kittiphun-rut/MCUPR-CANTEEN/docs/interface/tft-host-03-activity.png

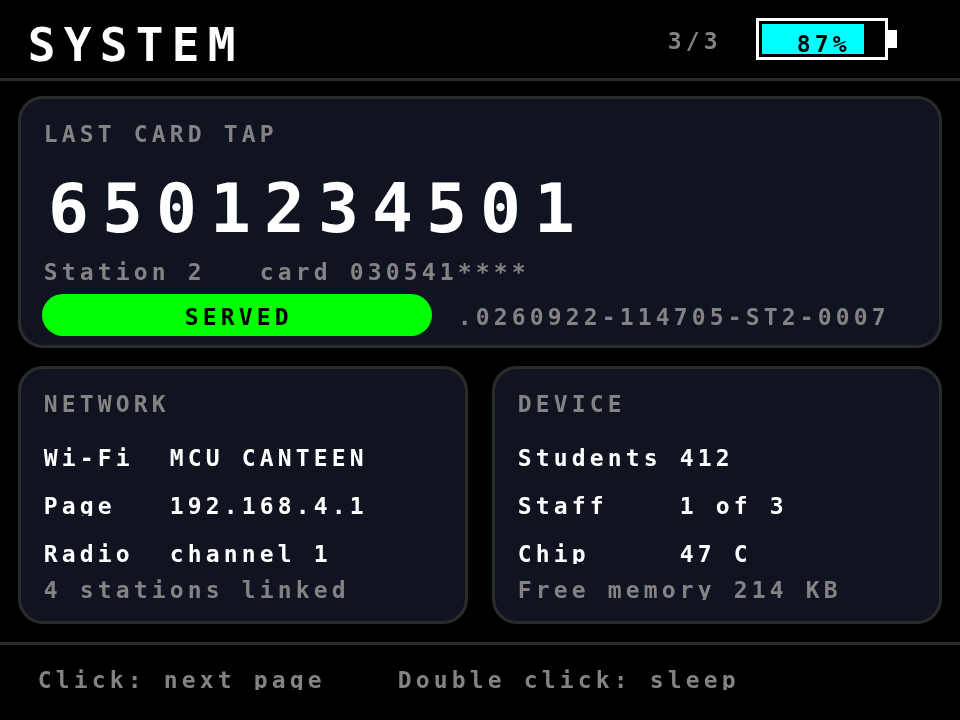
docs/interface/tft-host-03-activity.png
