kittiphun-rut/MCUPR-CANTEEN/docs/interface/tft-host-04-screensaver.png

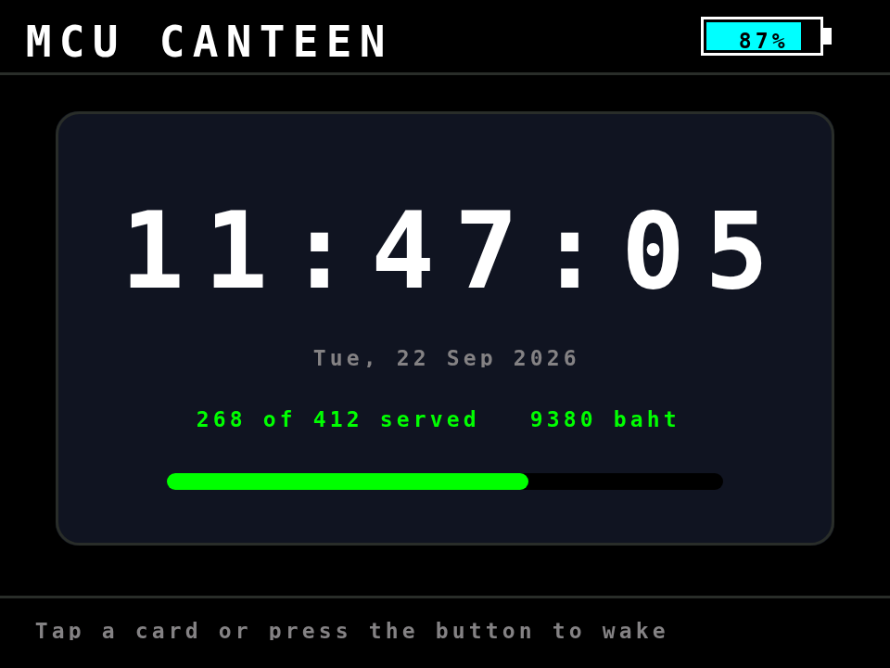
docs/interface/tft-host-04-screensaver.png
