kittiphun-rut/MCUPR-CANTEEN/docs/interface/tft-host-05-approved.png

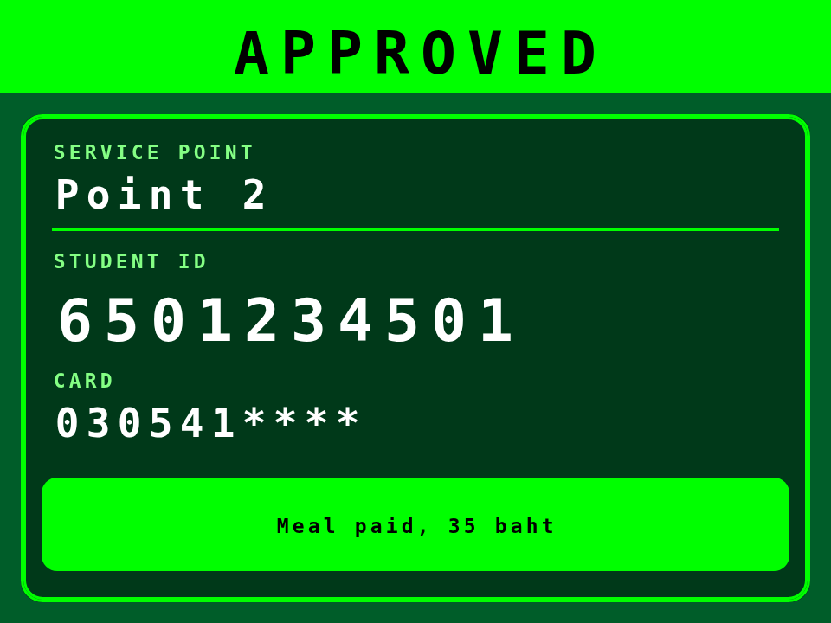
docs/interface/tft-host-05-approved.png
