kittiphun-rut/MCUPR-CANTEEN/docs/interface/tft-host-06-duplicate.png

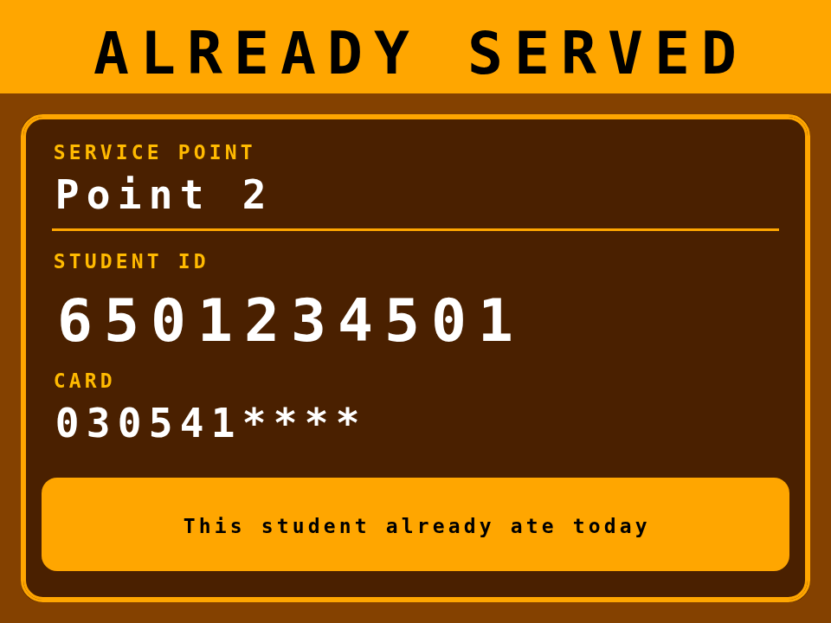
docs/interface/tft-host-06-duplicate.png
