kittiphun-rut/MCUPR-CANTEEN/docs/interface/tft-host-08-rejected.png

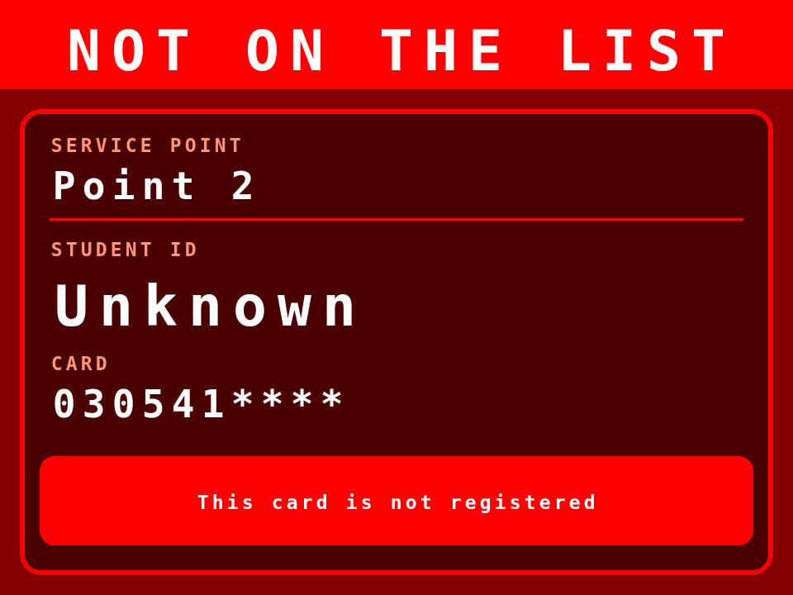
docs/interface/tft-host-08-rejected.png
