kittiphun-rut/MCUPR-CANTEEN/docs/interface/tft-host-09-bootnet-ok.png

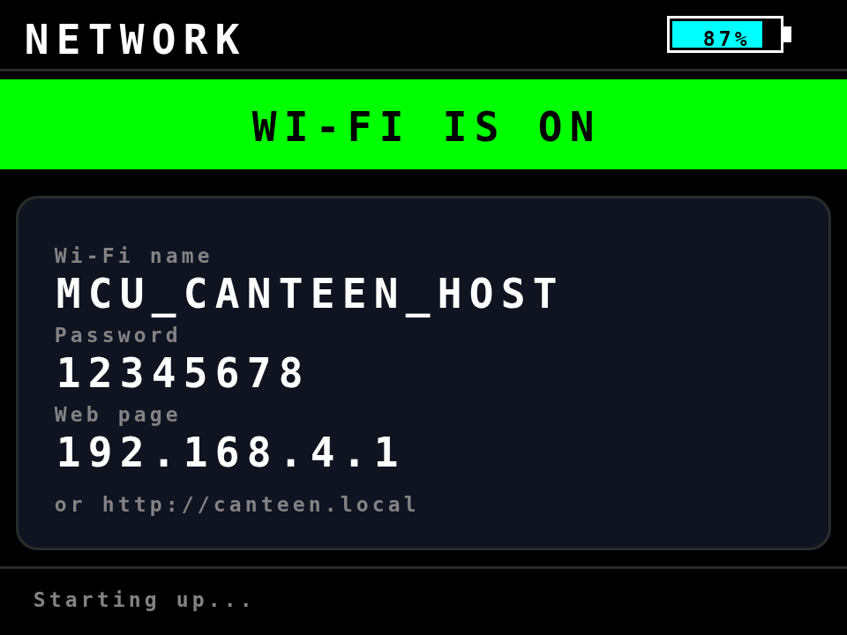
docs/interface/tft-host-09-bootnet-ok.png
