kittiphun-rut/MCUPR-CANTEEN/docs/interface/tft-host-10-bootnet-fail.png

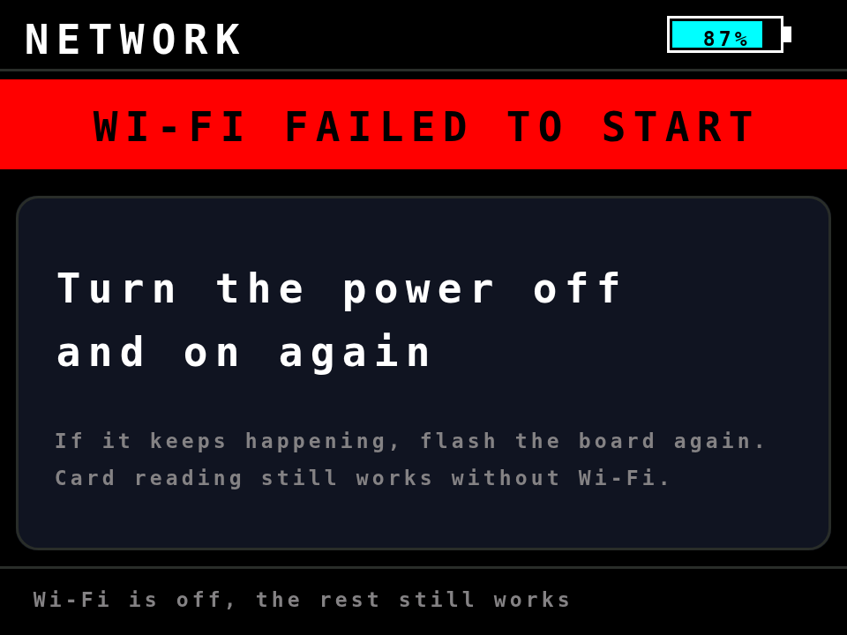
docs/interface/tft-host-10-bootnet-fail.png
