kittiphun-rut/MCUPR-CANTEEN/docs/interface/tft-host-11-credit.png

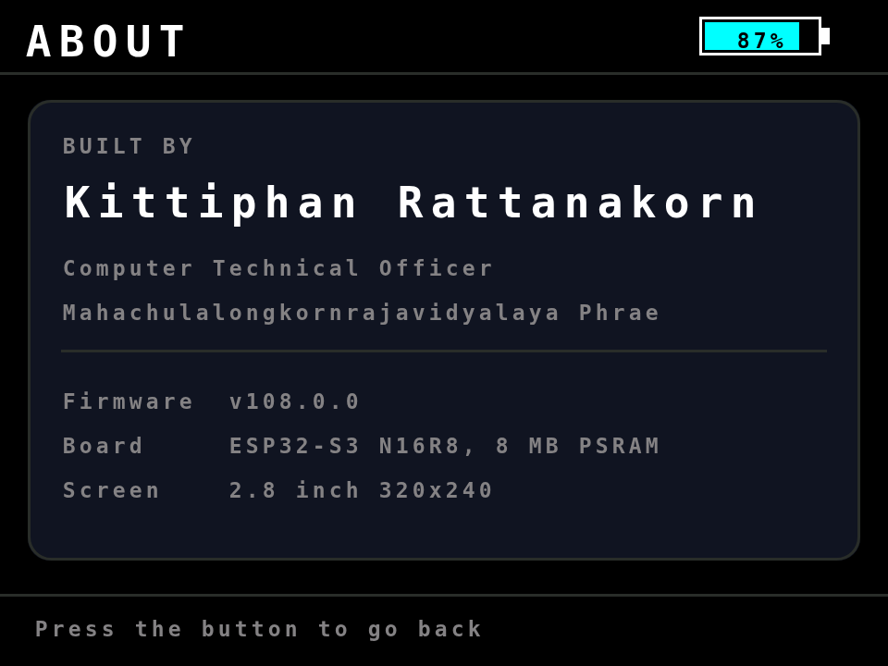
docs/interface/tft-host-11-credit.png
