kittiphun-rut/MCUPR-CANTEEN/docs/interface/tft-stn-03-diagnostics.png

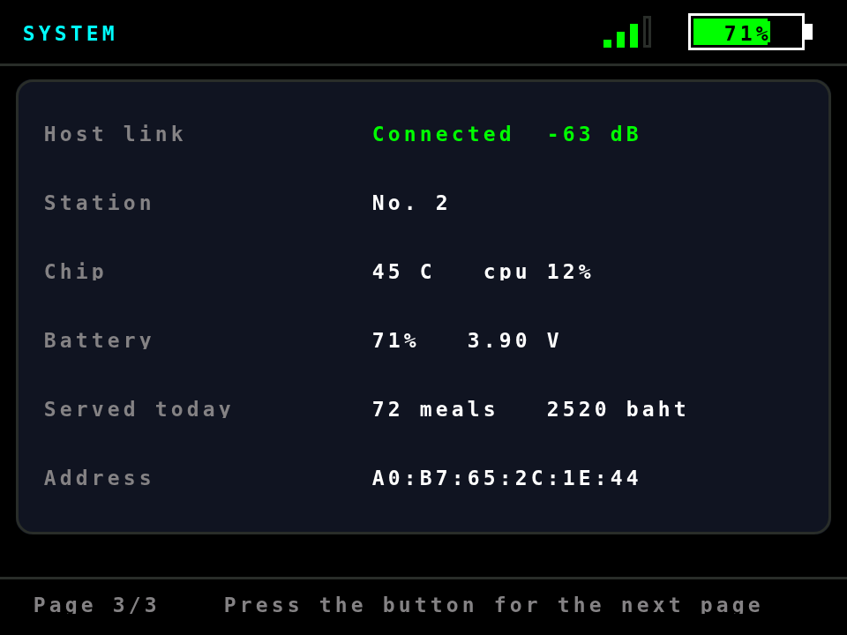
docs/interface/tft-stn-03-diagnostics.png
