kittiphun-rut/MCUPR-CANTEEN/docs/interface/tft-stn-04-screensaver.png

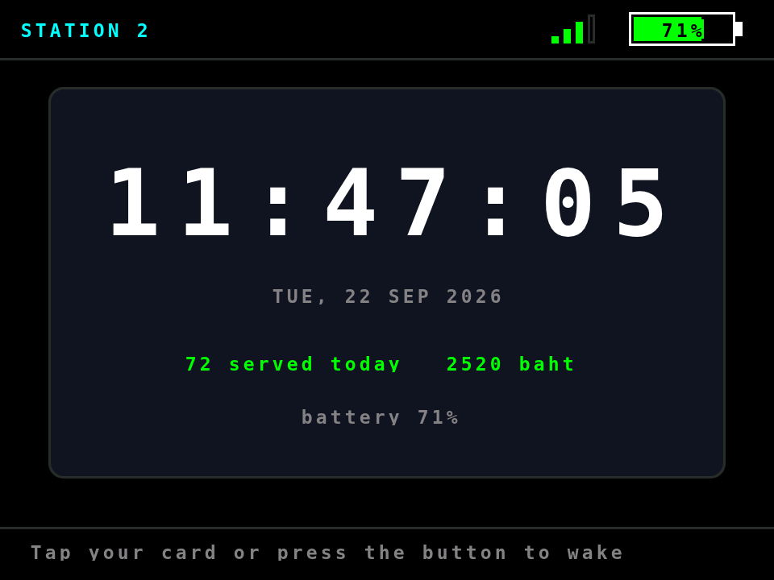
docs/interface/tft-stn-04-screensaver.png
