kittiphun-rut/MCUPR-CANTEEN/docs/interface/tft-stn-05-scanning.png

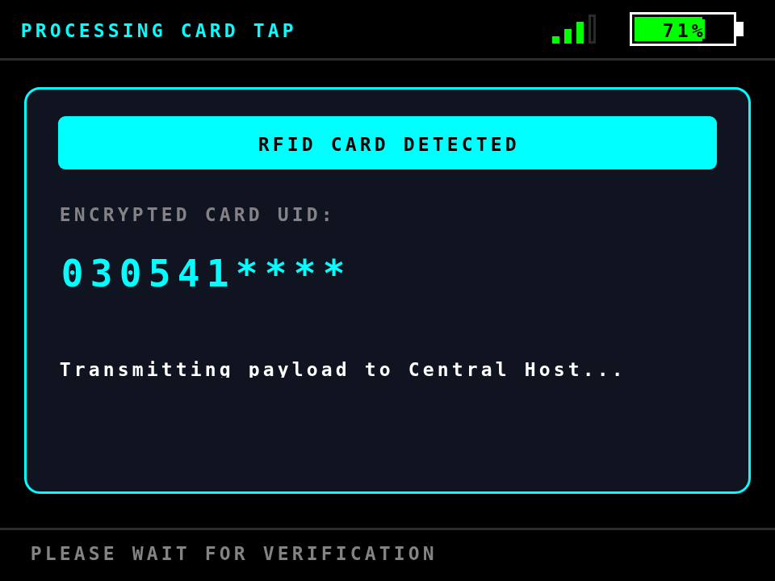
docs/interface/tft-stn-05-scanning.png
