kittiphun-rut/MCUPR-CANTEEN/docs/interface/tft-stn-07-duplicate.png

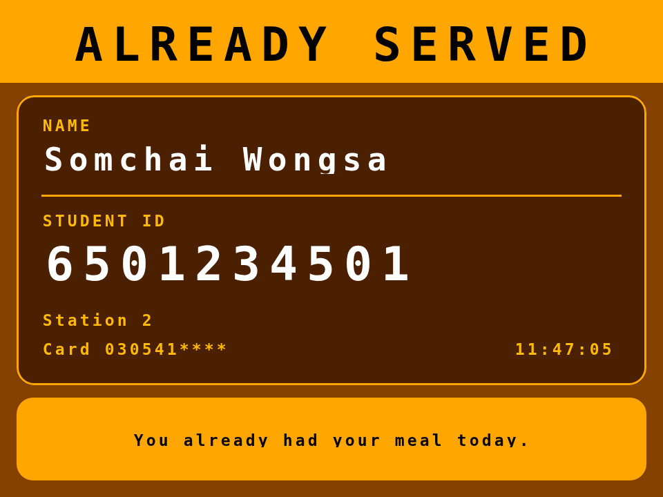
docs/interface/tft-stn-07-duplicate.png
