kittiphun-rut/MCUPR-CANTEEN/docs/interface/tft-stn-08-rejected.png

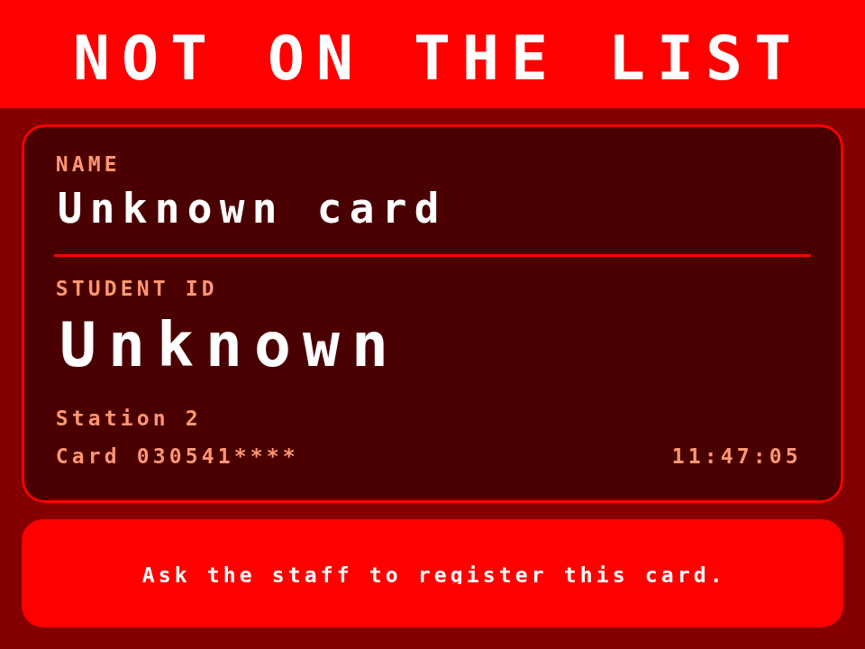
docs/interface/tft-stn-08-rejected.png
