kittiphun-rut/MCUPR-CANTEEN/docs/interface/tft-stn-09-offline.png

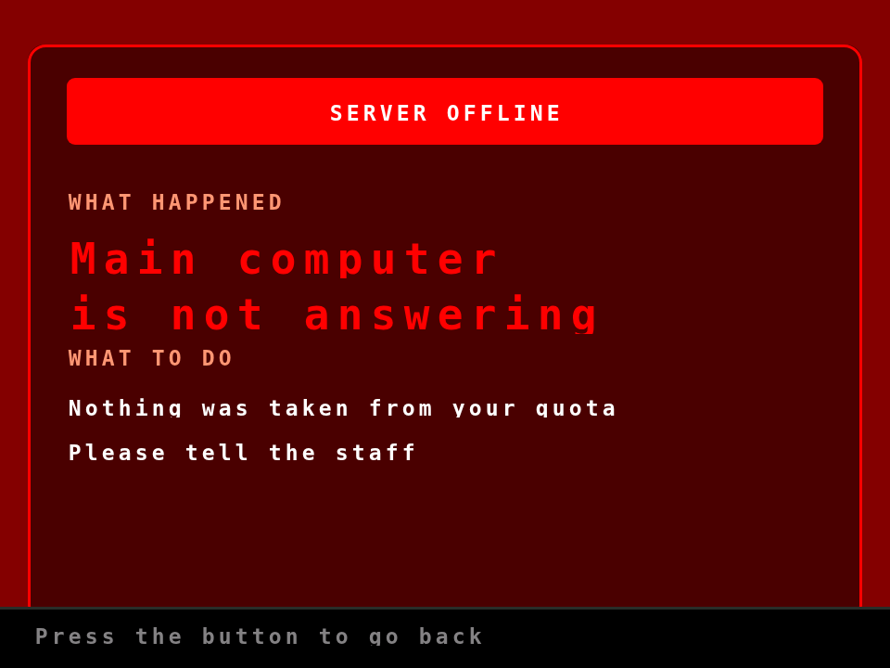
docs/interface/tft-stn-09-offline.png
