kittiphun-rut/MCUPR-CANTEEN/docs/interface/tft-stn-11-standby-light.png

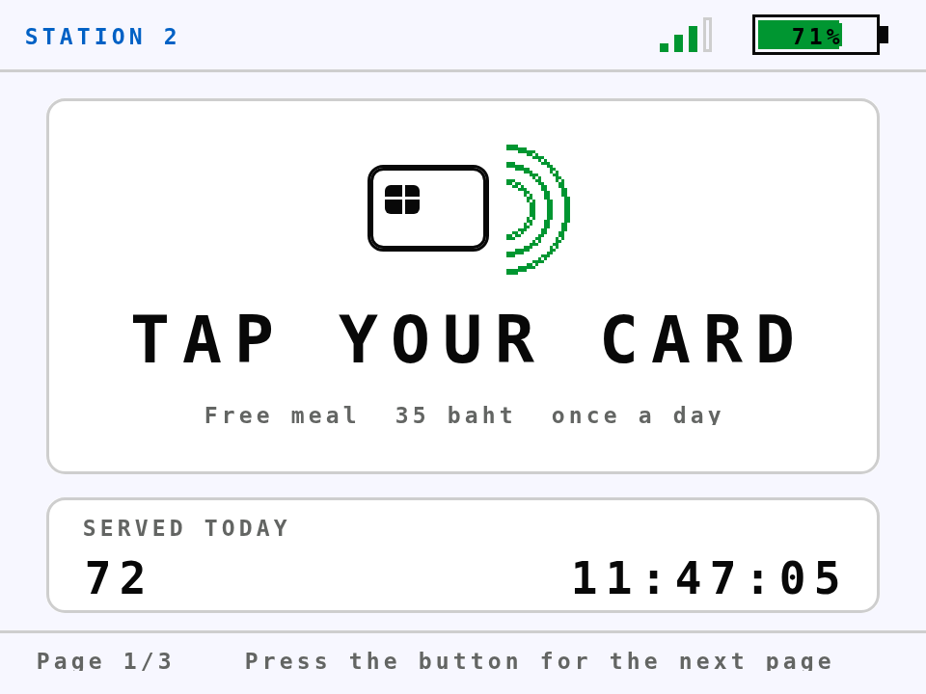
docs/interface/tft-stn-11-standby-light.png
