kittiphun-rut/MCUPR-CANTEEN/docs/interface/tft-stn-12-themelocked.png

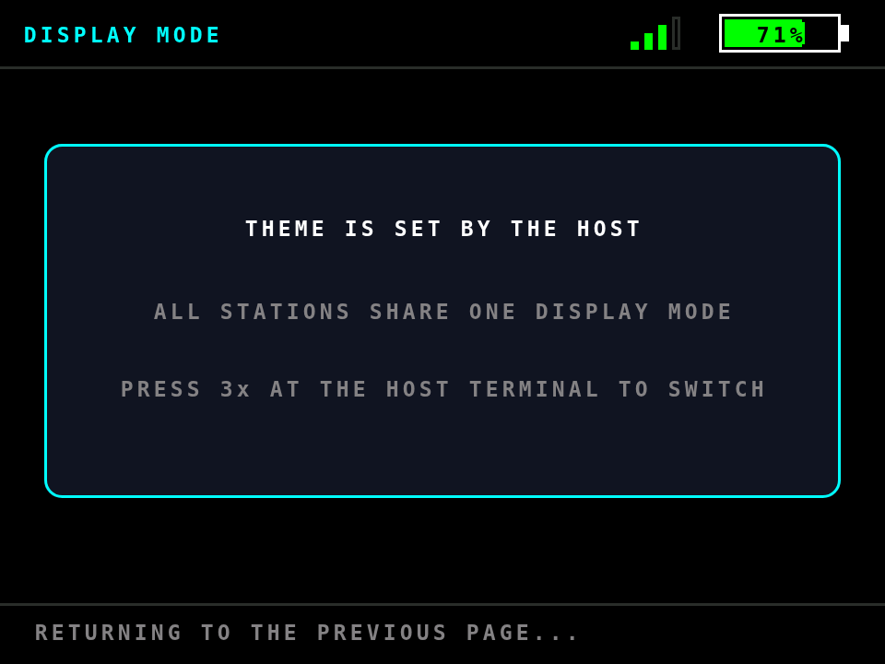
docs/interface/tft-stn-12-themelocked.png
