kittiphun-rut/MCUPR-CANTEEN/docs/interface/tft-stn-13-reader-down.png

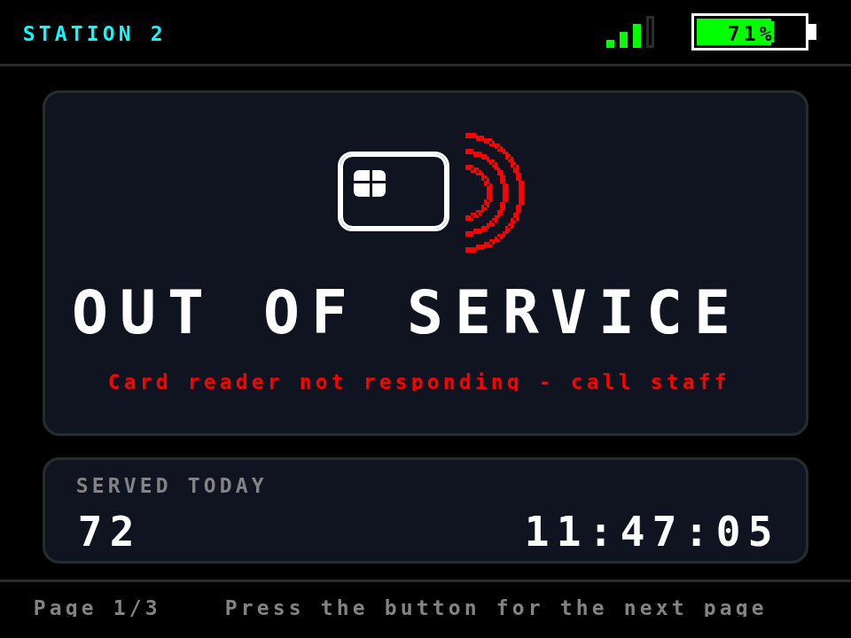
docs/interface/tft-stn-13-reader-down.png
