kittiphun-rut/MCUPR-CANTEEN/docs/interface/tft-stn-14-server-offline.png

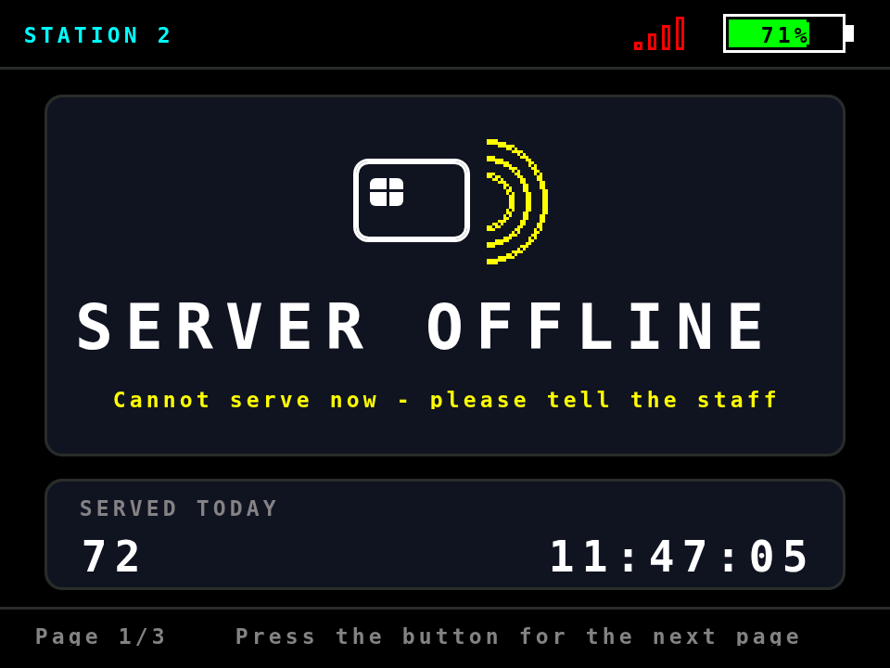
docs/interface/tft-stn-14-server-offline.png
