kittiphun-rut/MCUPR-CANTEEN/docs/interface/web-03-students.png

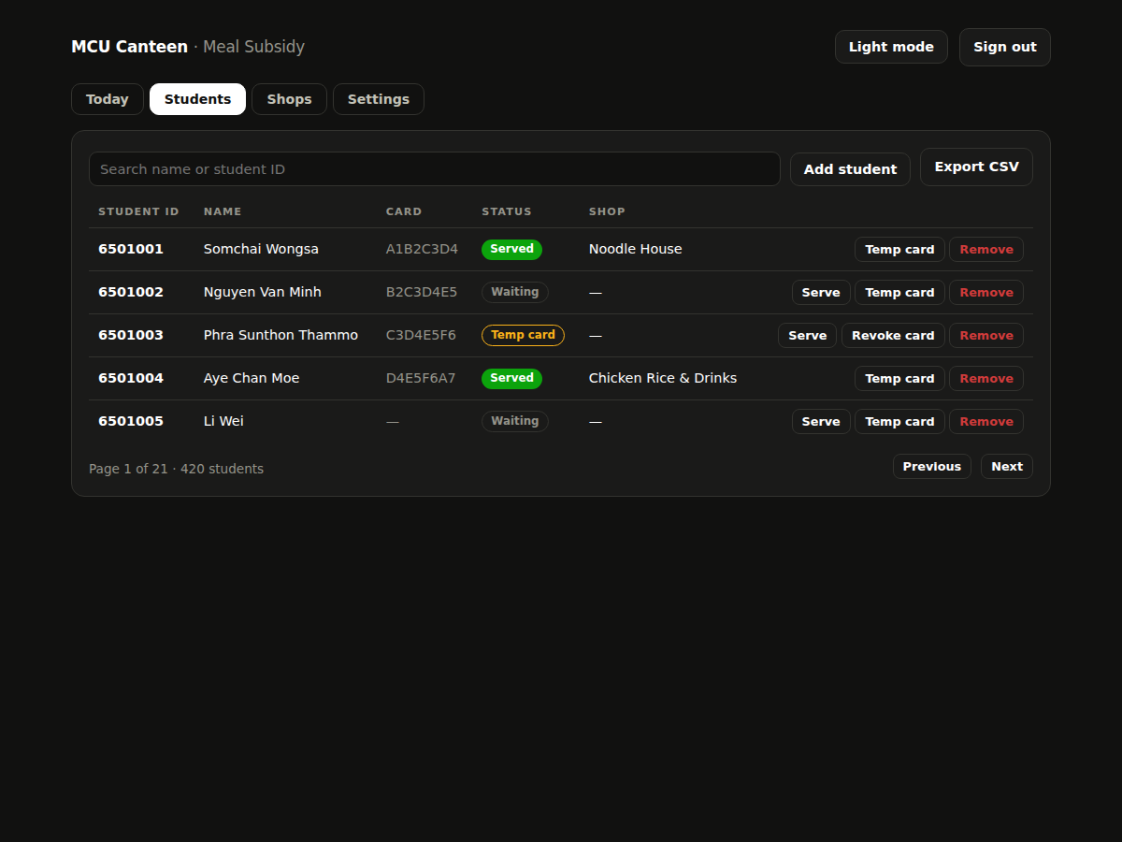
docs/interface/web-03-students.png
