kittiphun-rut/MCUPR-CANTEEN/docs/interface/web-04-shops.png

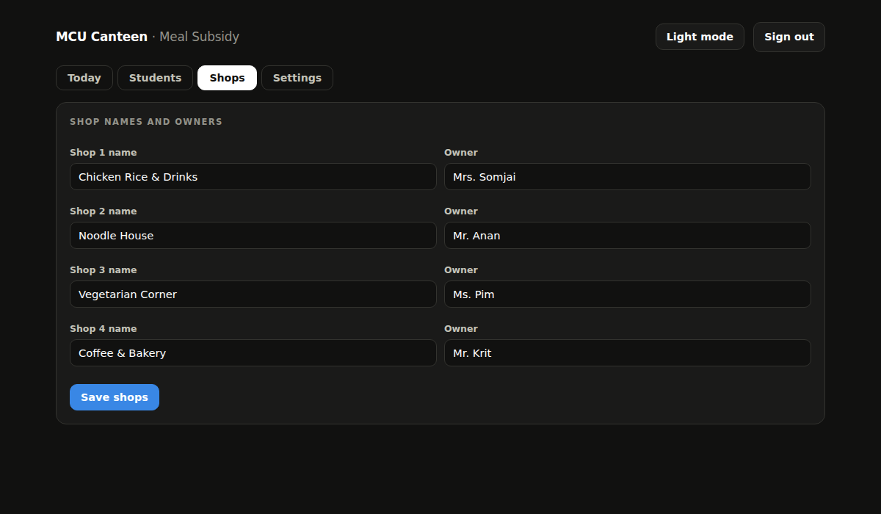
docs/interface/web-04-shops.png
