kittiphun-rut/MCUPR-CANTEEN/docs/interface/web-05-settings-light.png

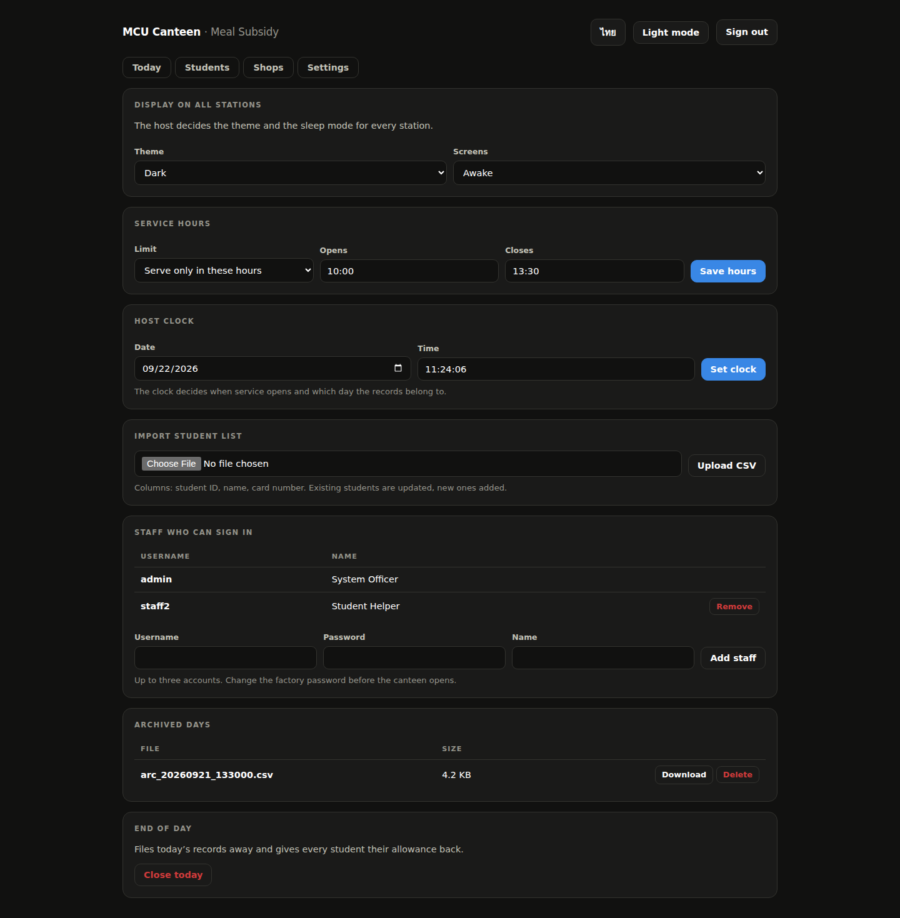
docs/interface/web-05-settings-light.png
