kittiphun-rut/MCUPR-CANTEEN/docs/interface/web-06-phone.png

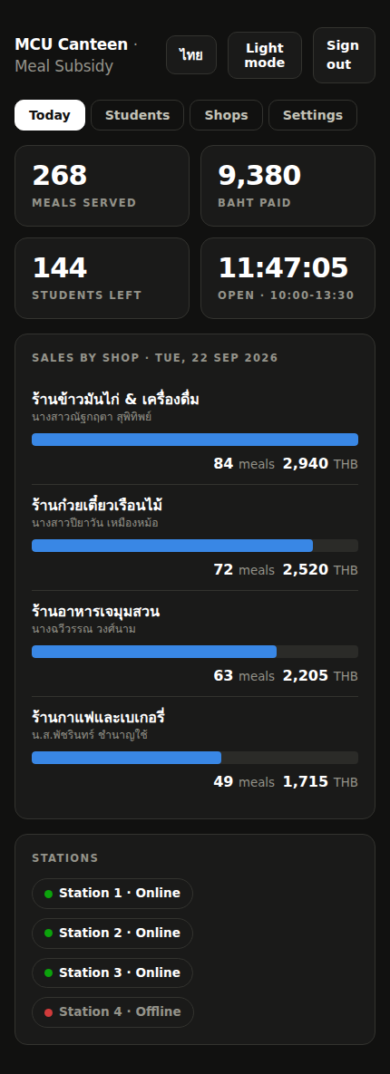
docs/interface/web-06-phone.png
