kittiphun-rut/MCUPR-CANTEEN/docs/interface/web-07-login.png

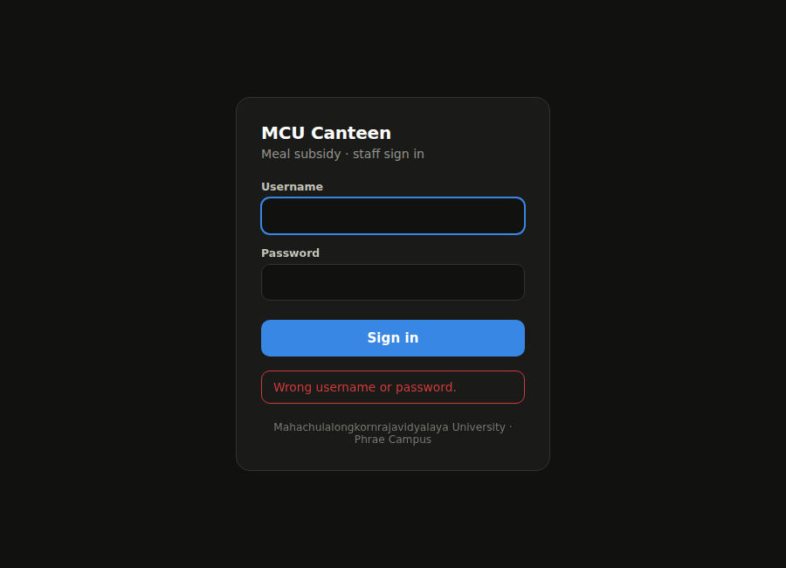
docs/interface/web-07-login.png
