kittiphun-rut/MCUPR-CANTEEN/docs/interface/web-08-today-th.png

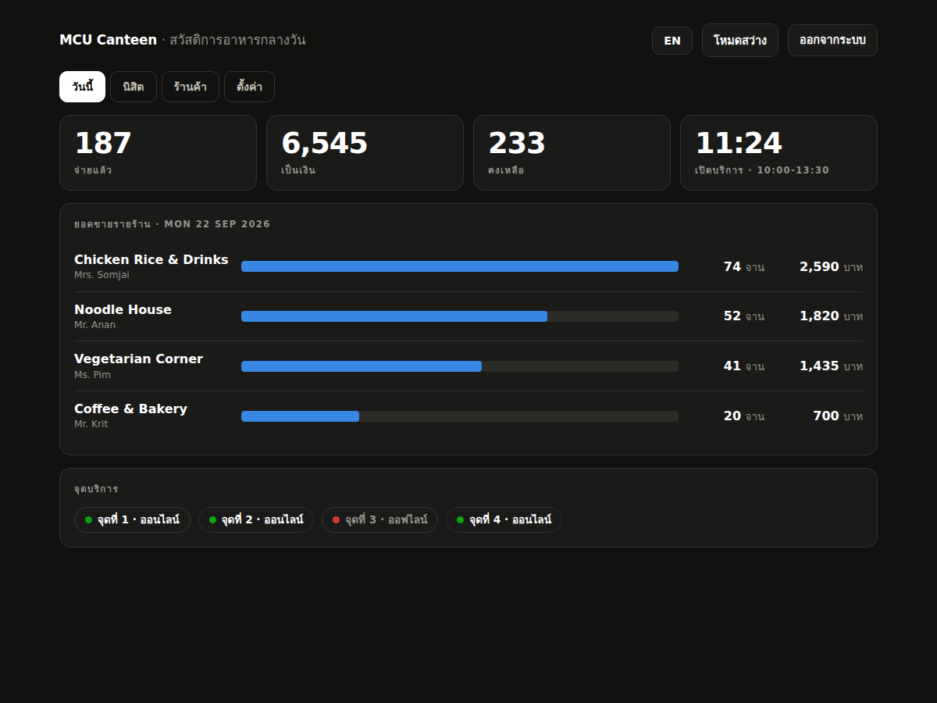
docs/interface/web-08-today-th.png
