kittiphun-rut/MCUPR-CANTEEN/docs/interface/web-10-settings-th.png

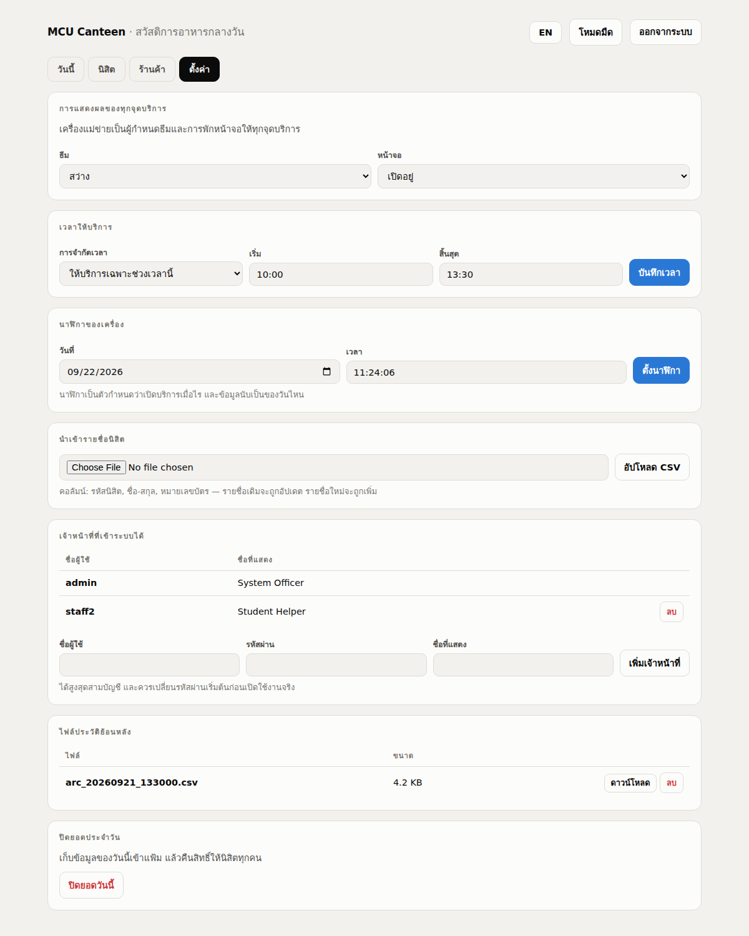
docs/interface/web-10-settings-th.png
