kittiphun-rut/MCUPR-CANTEEN/docs/interface/web-12-display-fullhd.png

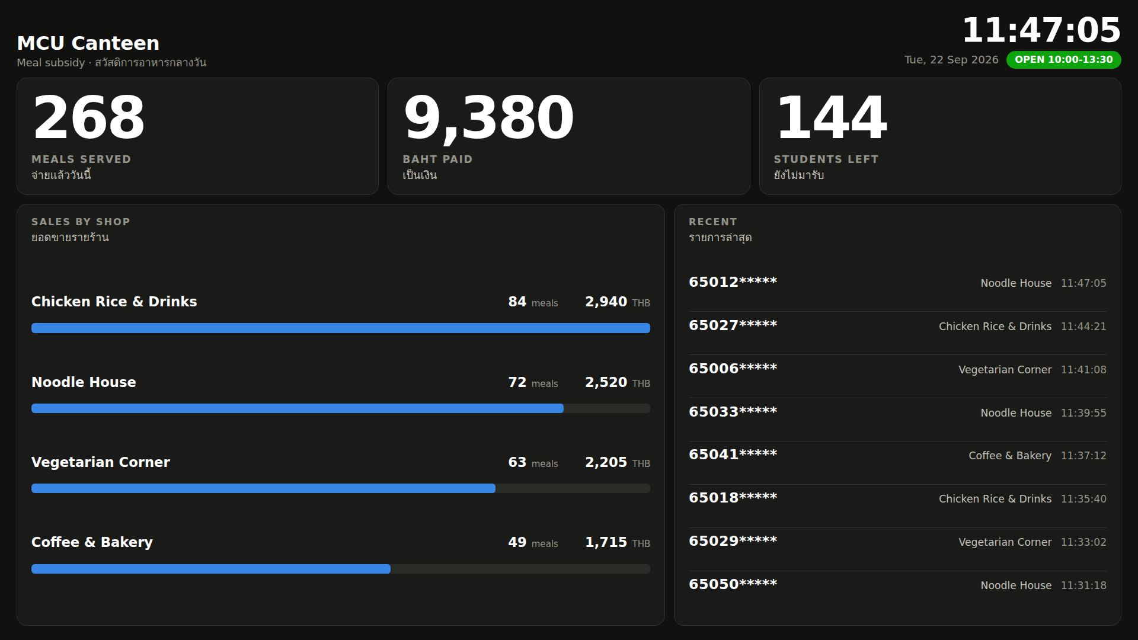
docs/interface/web-12-display-fullhd.png
