kittiphun-rut/MCUPR-CANTEEN/docs/interface/web-13-display-hd.png

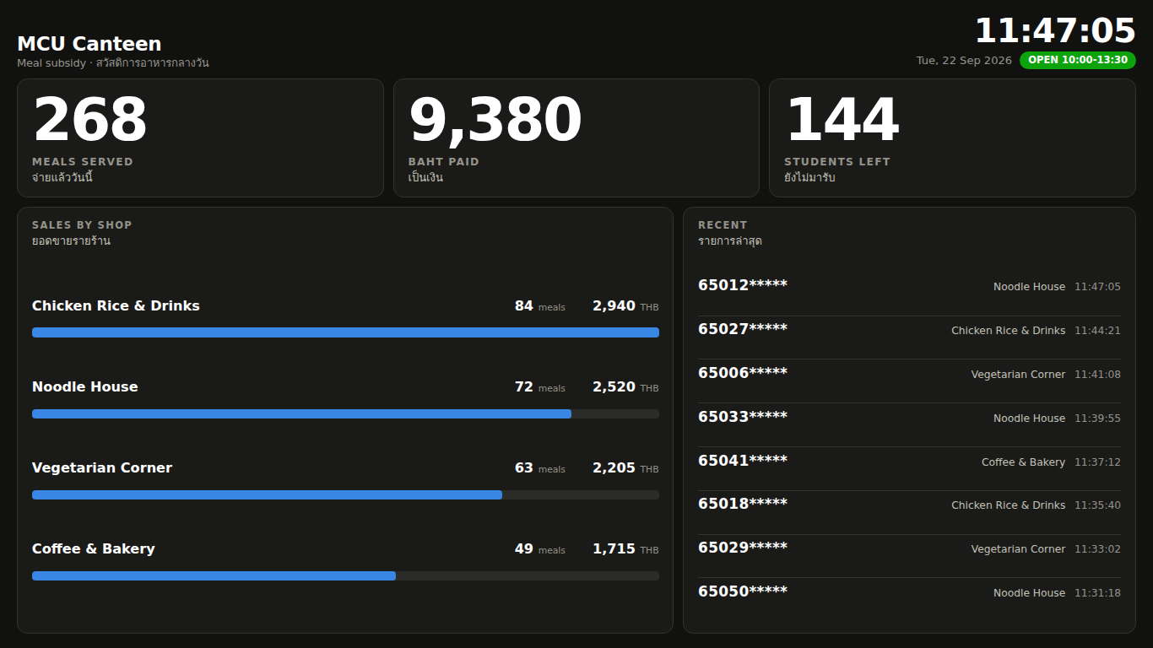
docs/interface/web-13-display-hd.png
