kittiphun-rut/MCUPR-CANTEEN/tools/screen-preview/shots/tft-host-07-timeclosed.png

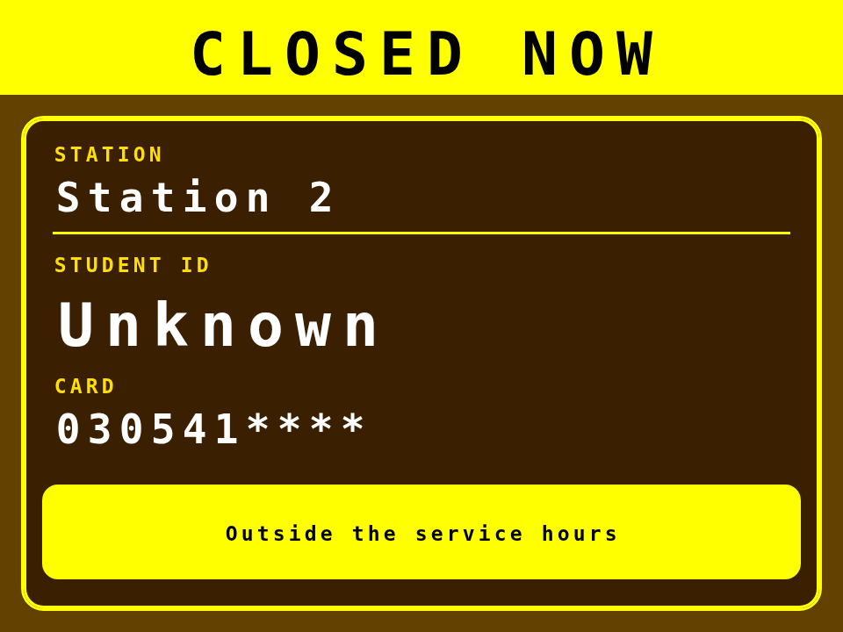
tools/screen-preview/shots/tft-host-07-timeclosed.png
