kittiphun-rut/MCUPR-CANTEEN/docs/interface/tft-stn-10-idsetup.png

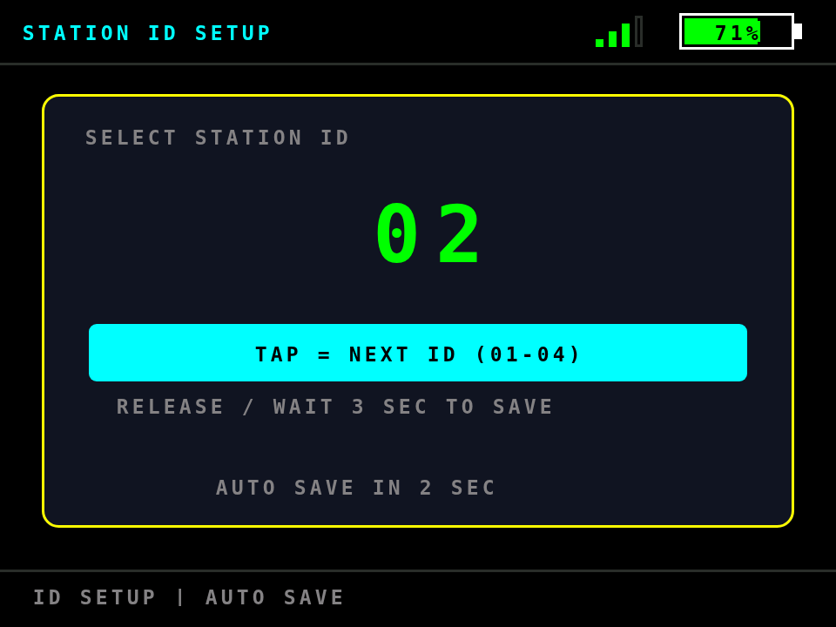
docs/interface/tft-stn-10-idsetup.png
