kittiphun-rut/MCUPR-CANTEEN/docs/interface/tft-stn-15-result-unknown.png

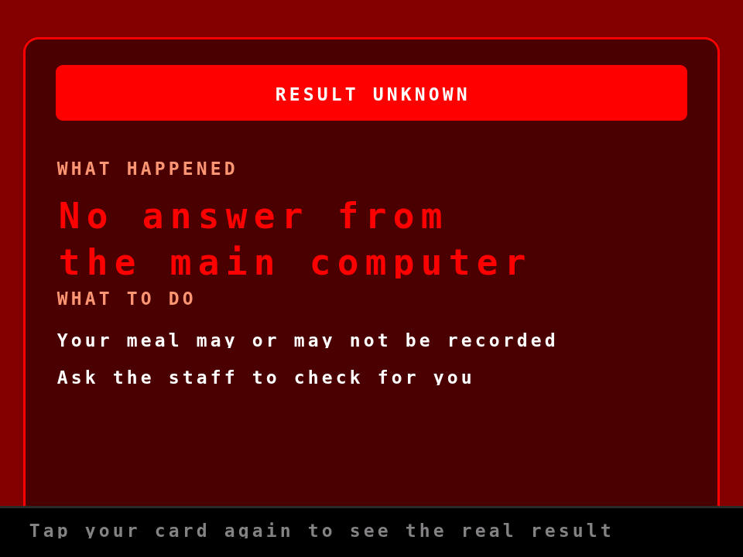
docs/interface/tft-stn-15-result-unknown.png
