kittiphun-rut/MCUPR-CANTEEN/hardware/kicad/Canteen_Station.kicad_sch

## KiCad design hardware/kicad/Canteen_Station.kicad_sch (2026-09-24)

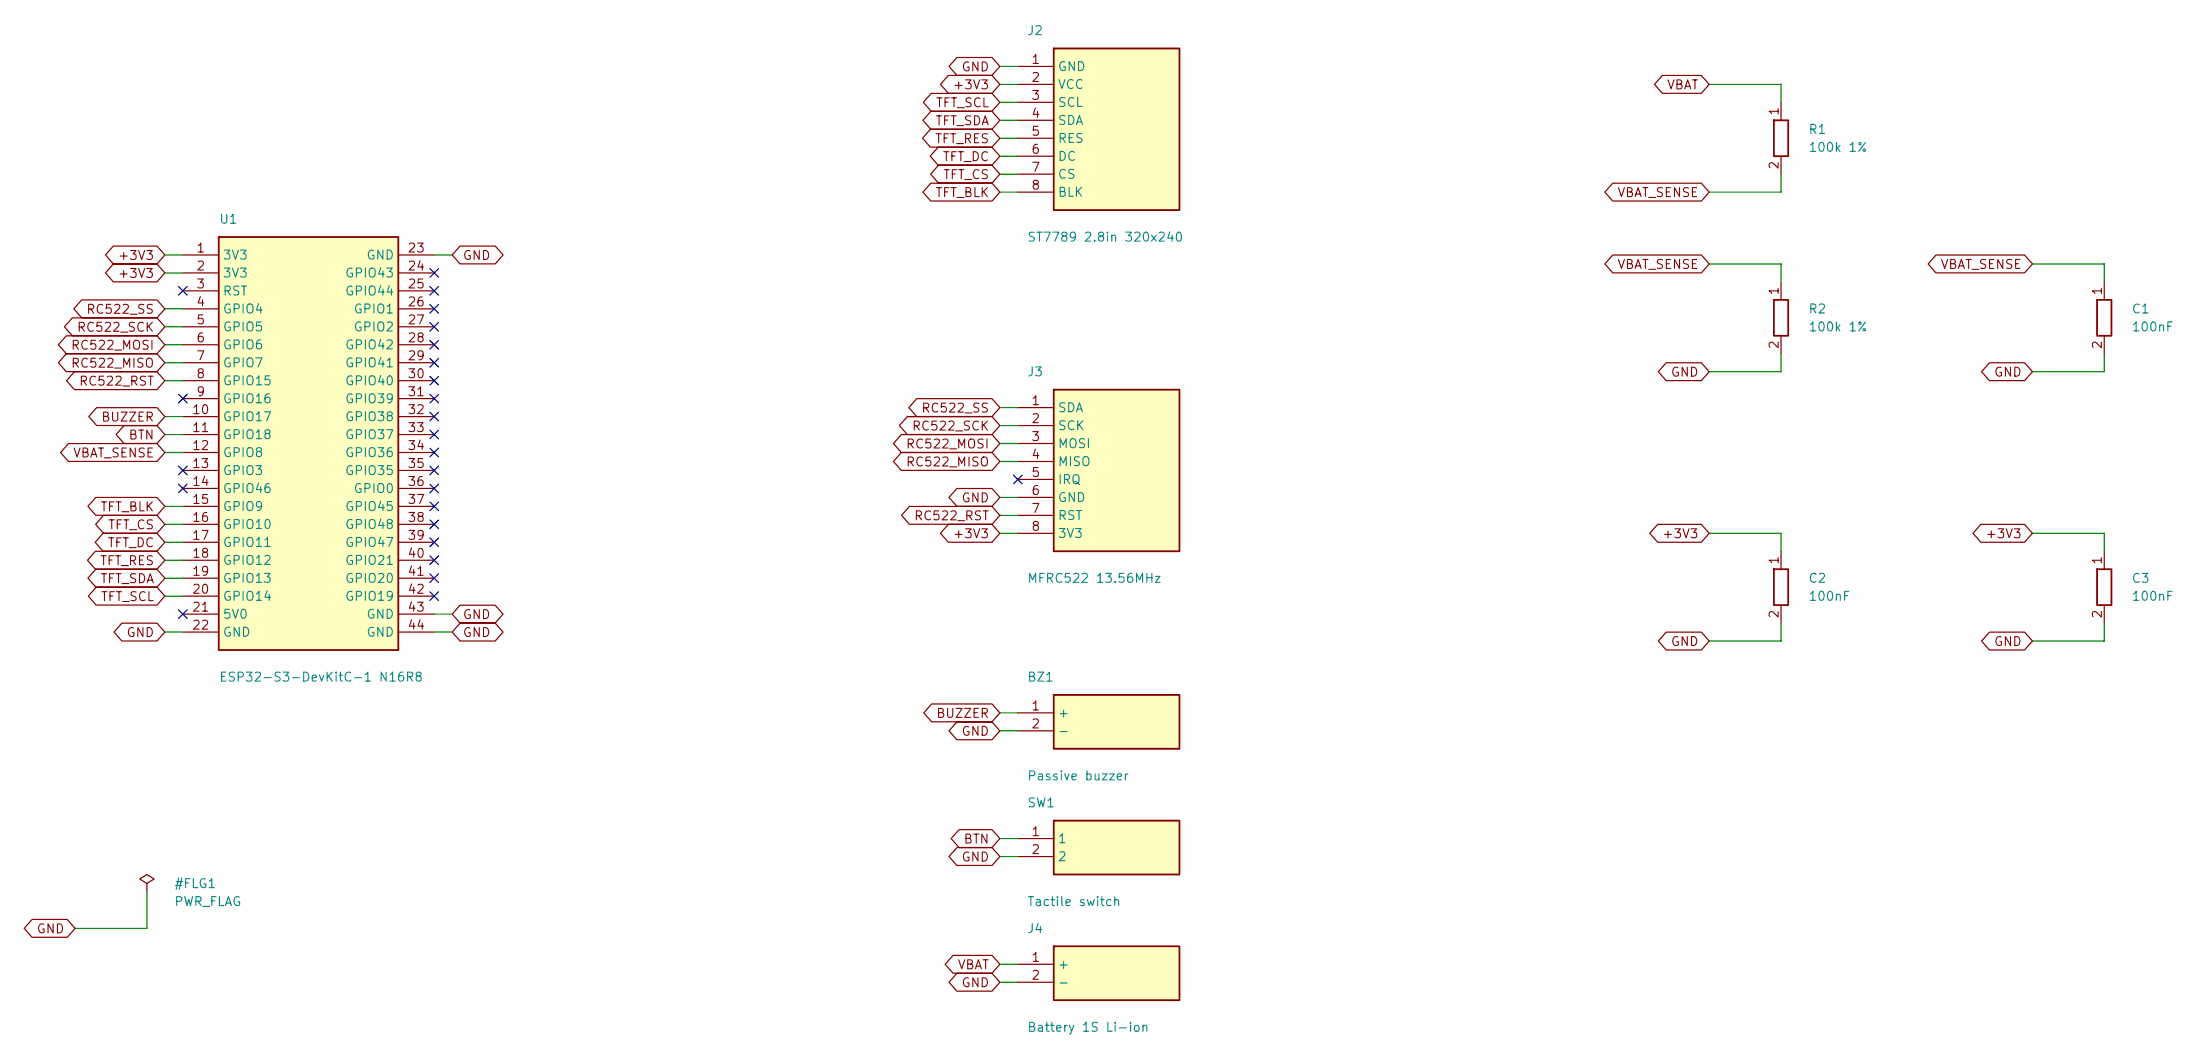
[picture p45: schematic Canteen_Station.kicad_sch]

Parts:
BZ1: Passive buzzer
C1, C2, C3: 100nF
J2: ST7789 2.8in 320x240
J3: MFRC522 13.56MHz
J4: Battery 1S Li-ion
R1, R2: 100k 1%
SW1: Tactile switch
U1: ESP32-S3-DevKitC-1 N16R8

Connections:
+3V3: C2.1, C3.1, J2.2 (VCC), J3.8 (3V3), U1.1 (3V3), U1.2 (3V3)
BTN: SW1.1, U1.11 (GPIO18)
BUZZER: BZ1.1 (+), U1.10 (GPIO17)
GND: BZ1.2 (-), C1.2, C2.2, C3.2, J2.1 (GND), J3.6 (GND), J4.2 (-), R2.2, SW1.2, U1.22 (GND), U1.23 (GND), U1.43 (GND), U1.44 (GND)
RC522_MISO: J3.4 (MISO), U1.7 (GPIO7)
RC522_MOSI: J3.3 (MOSI), U1.6 (GPIO6)
RC522_RST: J3.7 (RST), U1.8 (GPIO15)
RC522_SCK: J3.2 (SCK), U1.5 (GPIO5)
RC522_SS: J3.1 (SDA), U1.4 (GPIO4)
TFT_BLK: J2.8 (BLK), U1.15 (GPIO9)
TFT_CS: J2.7 (CS), U1.16 (GPIO10)
TFT_DC: J2.6 (DC), U1.17 (GPIO11)
TFT_RES: J2.5 (RES), U1.18 (GPIO12)
TFT_SCL: J2.3 (SCL), U1.20 (GPIO14)
TFT_SDA: J2.4 (SDA), U1.19 (GPIO13)
VBAT: J4.1 (+), R1.1
VBAT_SENSE: C1.1, R1.2, R2.1, U1.12 (GPIO8)
