kittiphun-rut/MCUPR-CANTEEN/Canteen_Host_Server/HostScreen.h

/**
 * @file      HostScreen.h
 * @brief     ทุกอย่างที่วาดลงจอ TFT ของเครื่องแม่ข่าย
 * @version   113.8.0
 * @date      2026-09-23
 * @author    Kittiphan Rattanakorn <kittiphun.rut@mcu.ac.th>
 *
 * @par Organization
 * มหาวิทยาลัยมหาจุฬาลงกรณราชวิทยาลัย วิทยาเขตแพร่
 *
 * @par Description
 * แยกออกมาจาก Canteen_Host_Server.ino เพื่อให้ไฟล์หลักสั้นและอ่านง่าย
 * นิสิตที่มารับช่วงดูแลต่อจะได้หาของเจอเร็วขึ้น
 *
 * มีสามหน้าหลักสลับด้วยปุ่มกด TODAY / SHOPS / SYSTEM
 * พร้อมหน้าพักจอ หน้าแจ้งผลการแตะบัตร หน้าแจ้งสถานะ Wi-Fi ตอนบูต และหน้าเครดิต
 *
 * ข้อความบนจอเป็นภาษาอังกฤษอย่างเดียว เพราะฟอนต์ในตัวไลบรารี Adafruit GFX
 * ไม่มีตัวอักษรไทย ส่วนหน้าเว็บเป็นสองภาษา
 *
 * @par Revision History
 * | Version | Date | Change |
 * |---|---|---|
 * | 113.8.0 | 2026-09-23 | เปลี่ยนคำว่า Point บนหน้าจอและหน้าเว็บเป็น Station ให้ตรงกับชื่อที่ใช้ทั้งระบบ ส่วนชื่อร้านยังใช้คำว่า Shop เหมือนเดิม |
 * | 113.5.0 | 2026-09-23 | จัดกึ่งกลางทุกบรรทัดบนหน้าพักจอ และให้วันที่กับช่วงเวลาอยู่บรรทัดฐานเดียวกัน |
 * | 113.4.0 | 2026-09-23 | กรองทุกข้อความให้เหลือเฉพาะ ASCII ก่อนวาด และตัดความยาวทุกช่องไม่ให้ล้นไปทับกัน |
 * | 113.3.0 | 2026-09-22 | เลิกล้างพื้นก่อนเขียนตัวอักษร ใช้การเขียนทับที่เดิมแทน จอไม่กะพริบทุกวินาทีแล้ว |
 * | 113.2.0 | 2026-09-22 | วาดซ้ำเฉพาะช่องที่ค่าเปลี่ยน ยอดรายร้านและยอดบนหน้าพักจออัปเดตเองแล้ว |
 * | 113.0.0 | 2026-09-22 | แยกออกมาจากไฟล์หลัก แล้วออกแบบหน้าจอใหม่ให้เรียบง่าย ตัวอักษรน้อย แบ่งช่องชัดเจน และรองรับสองโหมดสี |
 * | 107.0.1 | 2026-09-21 | ต้นฉบับที่ใช้เป็นจุดเริ่ม เก็บสำเนาไว้ที่ original/ |
 *
 * @warning  ถูก #include ท้ายไฟล์หลักก่อน setup() ห้ามย้ายขึ้นไปบนสุด
 * @note     Arduino IDE แสดงไฟล์นี้เป็นแท็บของสเก็ตช์เดียวกัน เปิดคู่กันได้เลย
 */

#pragma once

#include <stdarg.h>   // drawFixedText รับอาร์กิวเมนต์แบบ printf

// [113.4.0] เพิ่ม: บีบข้อความให้เหลือเฉพาะอักขระที่ฟอนต์ในตัวของจอวาดได้จริง
//
// ฟอนต์ของ Adafruit GFX มีแต่ ASCII ไบต์ตั้งแต่ 0x80 ขึ้นไปจะถูกวาดเป็นสัญลักษณ์มั่ว
// ภาษาไทยหนึ่งตัวกินสามไบต์ จึงกลายเป็นตัวประหลาดสามตัว และ **กินที่กว้างกว่าที่นับไว้
// สามเท่า** ข้อความจึงล้นกรอบไปทับของข้างเคียง เห็นเป็นอักษรซ้อนกัน
//
// ตัดทิ้งไปเลยแทนการแทนด้วยเครื่องหมายคำถาม เพราะชื่อไทยล้วนจะได้เหลือสตริงว่าง
// แล้วให้ผู้เรียกถอยไปใช้ชื่อภาษาอังกฤษสำรองได้ถูกต้อง
// [113.5.0] เพิ่ม: วาดข้อความให้อยู่กึ่งกลางแกน x โดยไม่ต้องล้างพื้นก่อน
//
// drawFixedText() เติมช่องว่างท้ายอย่างเดียว ข้อความจึงชิดซ้ายของช่องเสมอ
// พอเอาไปใช้แทนบรรทัดที่เคยจัดกึ่งกลาง ข้อความเลยเยื้องไปทางซ้าย
//
// ตัวนี้เติมช่องว่างทั้งสองข้างให้ช่องกว้างคงที่ ข้อความจึงอยู่กึ่งกลางจริง
// และช่องว่างที่เติมก็ลบของเดิมที่ยาวกว่าไปพร้อมกัน ไม่ต้องล้างพื้น ไม่กะพริบ
//
// cx คือจุดกึ่งกลางที่ต้องการ ส่วน width คือความกว้างของช่องเป็นจำนวนตัวอักษร
// ต้องกว้างพอสำหรับค่าที่ยาวที่สุดที่เป็นไปได้ ไม่งั้นจะถูกตัด
void drawCenteredText(int cx, int y, uint8_t size, uint16_t fg, uint16_t bg,
                      int width, const char* fmt, ...) {
  if (width < 1) width = 1;
  if (width > 70) width = 70;

  char raw[80];
  va_list args;
  va_start(args, fmt);
  vsnprintf(raw, sizeof(raw), fmt, args);
  va_end(args);

  int len = (int)strlen(raw);
  if (len > width) { len = width; raw[width] = '\0'; }
  int left = (width - len) / 2;

  char padded[80];
  memset(padded, ' ', sizeof(padded));
  memcpy(padded + left, raw, len);
  padded[width] = '\0';

  tft.setTextSize(size);
  tft.setTextColor(fg, bg);
  tft.setCursor(cx - (width * 6 * (int)size) / 2, y);
  tft.print(padded);
}


String asciiOnly(const String &raw) {
  String out;
  out.reserve(raw.length());
  for (unsigned int i = 0; i < raw.length(); i++) {
    uint8_t c = (uint8_t)raw[i];
    if (c >= 0x20 && c < 0x7F) out += (char)c;
  }
  out.trim();
  return out;
}


// [113.3.0] เพิ่ม: วาดข้อความทับที่เดิมโดยไม่ต้องล้างพื้นก่อน
//
// ต้นเหตุของการกะพริบคือลำดับ "ล้างพื้น แล้วค่อยเขียนตัวอักษร"
// ระหว่างสองจังหวะนั้นจอว่างเปล่าจริง ๆ ตาคนจึงเห็นเป็นการกะพริบทุกวินาที
//
// Adafruit GFX ลงสีพื้นให้ทุกตัวอักษรอยู่แล้วเมื่อกำหนดสีพื้นไว้ด้วย
// (setTextColor สองอาร์กิวเมนต์) ข้อความใหม่จึงเขียนทับของเดิมได้ในจังหวะเดียว
// ไม่มีช่วงที่จอว่าง ไม่ต้องเรียก fillRect เลย
//
// เงื่อนไขเดียวคือความยาวต้องคงที่ จึงเติมช่องว่างท้ายข้อความให้ครบ width เสมอ
// ไม่งั้นตัวอักษรเก่าที่ยาวกว่าจะค้างอยู่ เช่น 187 เปลี่ยนเป็น 9 แล้วเหลือ 87
// ใช้ %-*s ซึ่งเติมให้ครบแต่ไม่ตัดทิ้ง ค่าที่ยาวเกินคาดจึงยังแสดงครบ ไม่โกหกตัวเลข
void drawFixedText(int x, int y, uint8_t size, uint16_t fg, uint16_t bg,
                   int width, const char* fmt, ...) {
  char raw[64];
  va_list args;
  va_start(args, fmt);
  vsnprintf(raw, sizeof(raw), fmt, args);
  va_end(args);

  // ตัดให้ยาวเท่า width พอดีเสมอ ไม่ใช่แค่เติมให้ครบ
  // ถ้าปล่อยให้ยาวเกินได้ ข้อความจะล้นไปทับช่องข้างเคียง และพอรอบหน้าค่าสั้นลง
  // ช่องว่างที่เติมก็ลบของเก่าไม่หมด เหลือเป็นอักษรซ้อนกันค้างอยู่
  // ทุกช่องจึงถูกกำหนดความกว้างเผื่อไว้แล้วให้ค่าจริงยาวไม่ถึง
  char padded[72];
  snprintf(padded, sizeof(padded), "%-*.*s", width, width, raw);

  tft.setTextSize(size);
  tft.setTextColor(fg, bg);
  tft.setCursor(x, y);
  tft.print(padded);
}


// --- ชิ้นส่วนพื้นฐาน: การ์ด ป้าย แถบบน แถบล่าง ไอคอนแบตเตอรี่ ---
void drawBentoCard(int x, int y, int w, int h, uint16_t borderColor, uint16_t bgColor) {
  tft.fillRoundRect(x, y, w, h, 8, bgColor);
  tft.drawRoundRect(x, y, w, h, 8, borderColor);
}

void drawBentoPillBadge(int x, int y, int w, int h, const char* text, uint16_t fgColor, uint16_t bgColor) {
  tft.fillRoundRect(x, y, w, h, h / 2, bgColor);
  tft.setTextColor(fgColor, bgColor);
  tft.setTextSize(1);
  int textLen = strlen(text) * 6;
  int posX = x + (w - textLen) / 2;
  tft.setCursor(max(x + 2, posX), y + (h - 8) / 2);
  tft.print(text);
}

void drawHostBatteryHUD(int x, int y) {
  float volt = readHostBatteryVoltage();
  int pct = getHostBatteryPercentage(volt);

  tft.fillRect(x, y, 54, 18, getTftBg());
  tft.drawRect(x, y + 2, 44, 14, getTftTextMain());
  tft.fillRect(x + 44, y + 6, 3, 6, getTftTextMain());

  int fillWidth = (pct * 40) / 100;
  if (fillWidth < 1 && pct > 0) fillWidth = 1;

  uint16_t fillColor = (pct > 20) ? getTftAccentGreen() : getTftAccentRose();
  if (volt > 4.0f) fillColor = getTftAccentCyan();

  tft.fillRect(x + 2, y + 4, fillWidth, 10, fillColor);

  String pctStr = String(pct) + "%";
  int textWidth = pctStr.length() * 6;
  int textX = x + 2 + (40 - textWidth) / 2; 
  int textY = y + 6;

  tft.setTextSize(1);
  uint16_t textBg = (fillWidth > 22) ? fillColor : getTftBg();
  tft.setTextColor((fillWidth > 22) ? 0x0000 : getTftTextMain(), textBg);
  tft.setCursor(textX, textY);
  tft.print(pctStr);
}

void drawMiniBattery(int x, int y, int pct) {
  tft.fillRect(x, y, 26, 12, getTftCardBg());
  tft.drawRect(x, y, 22, 12, getTftTextMain());
  tft.fillRect(x + 22, y + 4, 2, 4, getTftTextMain());
  int fillW = (pct * 18) / 100;
  if (fillW < 1 && pct > 0) fillW = 1;
  uint16_t fColor = (pct > 20) ? getTftAccentGreen() : getTftAccentRose();
  tft.fillRect(x + 2, y + 2, fillW, 8, fColor);
}

void drawHostTopBar(String title, int pageNo) {
  tft.fillRect(0, 0, 320, 26, getTftBg());
  tft.drawFastHLine(0, 26, 320, getTftCardBorder());
  tft.setTextColor(getTftTextMain(), getTftBg());
  tft.setTextSize(2);
  tft.setCursor(8, 6);
  tft.print(title);
  if (pageNo > 0) {
    char tag[8];
    snprintf(tag, sizeof(tag), "%d/%d", pageNo, TOTAL_PAGES);
    tft.setTextSize(1);
    tft.setTextColor(getTftTextMuted(), getTftBg());
    tft.setCursor(222, 9);
    tft.print(tag);
  }
  drawHostBatteryHUD(252, 4);
}

void drawBentoBottomBar(String instruction) {
  tft.fillRect(0, 214, 320, 26, getTftBg());
  tft.drawFastHLine(0, 214, 320, getTftCardBorder());
  tft.setTextColor(getTftTextMuted(), getTftBg());
  tft.setTextSize(1);
  tft.setCursor(12, 222);
  tft.println(instruction);
}

// --- แอนิเมชันตอนบูต ---
void playBootAnimation() {
  setLedColor(0, 30, 60);
  tft.fillScreen(ST77XX_BLACK);
  int centerX = 160; int centerY = 110;
  for (int r = 10; r <= 85; r += 9) {
    tft.drawCircle(centerX, centerY, r, ST77XX_BLUE);
    tft.drawCircle(centerX, centerY, r + 2, ST77XX_CYAN);
    delay(20);
  }
  tft.fillScreen(ST77XX_BLACK);
  tft.drawRect(2, 2, 316, 236, ST77XX_BLUE);
  tft.drawRect(4, 4, 312, 232, ST77XX_CYAN);
  
  tft.setTextColor(ST77XX_YELLOW, ST77XX_BLACK);
  tft.setTextSize(2);
  tft.setCursor(22, 30);
  tft.println("MCU CANTEEN");
  
  tft.setTextColor(ST77XX_WHITE, ST77XX_BLACK);
  tft.setTextSize(1);
  tft.setCursor(44, 60);
  tft.println("Meal subsidy system");

  tft.setTextColor(ST77XX_GREEN, ST77XX_BLACK);
  tft.setCursor(68, 76);
  tft.printf("ESP32-S3 N16R8 | PSRAM: %d MB\n", ESP.getPsramSize() / 1024 / 1024);

  int barX = 40; int barY = 120; int barW = 240; int barH = 16;
  tft.drawRoundRect(barX - 2, barY - 2, barW + 4, barH + 4, 4, ST77XX_WHITE);
  const char* loadSteps[] = {
    "Opening storage...",
    "Loading student list...",
    "Checking the clock...",
    "Starting Wi-Fi...",
    "Ready"
  };
  for (int step = 0; step < 5; step++) {
    tft.fillRect(barX, barY + 28, barW, 14, ST77XX_BLACK);
    tft.setTextColor(ST77XX_CYAN, ST77XX_BLACK);
    tft.setTextSize(1);
    tft.setCursor(barX, barY + 28);
    tft.println(loadSteps[step]);
    int targetW = (barW * (step + 1)) / 5;
    tft.fillRoundRect(barX, barY, targetW, barH, 2, ST77XX_GREEN);
    delay(140);
  }
  soundWelcome();
  ledStandby();
  delay(200);
}

// หน้าบอกสถานะเครือข่ายตอนบูต ค้างไว้สามวินาที
// มีไว้เพราะเคยเจอปัญหาชื่อ Wi-Fi ไม่โผล่มา แล้วไม่มีอะไรบนเครื่องบอกเลยว่าเกิดอะไรขึ้น
// [113.0.0] เพิ่ม: บอกสถานะ Wi-Fi ตอนบูต ค้างไว้สามวินาที
//           เคยเจอปัญหาชื่อ Wi-Fi ไม่โผล่มา แล้วไม่มีอะไรบนเครื่องบอกว่าเกิดอะไรขึ้น
void showBootNetworkStatus() {
  tft.fillScreen(getTftBg());
  drawHostTopBar("NETWORK");

  uint16_t tone = hostApReady ? getTftAccentGreen() : getTftAccentRose();
  tft.fillRect(0, 30, 320, 34, tone);
  const char* head = hostApReady ? "WI-FI IS ON" : "WI-FI FAILED TO START";
  tft.setTextSize(2);
  tft.setTextColor(isTftDarkMode ? 0x0000 : BENTO_WHITE, tone);
  tft.setCursor(max(4, (320 - (int)strlen(head) * 12) / 2), 39);
  tft.print(head);

  drawBentoCard(6, 74, 308, 134, getTftCardBorder(), getTftCardBg());
  tft.setTextSize(1);
  if (hostApReady) {
    tft.setTextColor(getTftTextMuted(), getTftCardBg());
    tft.setCursor(20, 92);  tft.print("Wi-Fi name");
    tft.setCursor(20, 122); tft.print("Password");
    tft.setCursor(20, 152); tft.print("Web page");
    tft.setTextColor(getTftTextMain(), getTftCardBg());
    tft.setTextSize(2);
    tft.setCursor(20, 102); tft.print(default_ap_ssid);
    tft.setCursor(20, 132); tft.print(default_ap_pass);
    tft.setCursor(20, 162); tft.print(WiFi.softAPIP().toString());
    tft.setTextSize(1);
    tft.setTextColor(getTftTextMuted(), getTftCardBg());
    tft.setCursor(20, 186); tft.printf("or http://%s.local", mdns_hostname);
  } else {
    tft.setTextColor(getTftTextMain(), getTftCardBg());
    tft.setTextSize(2);
    tft.setCursor(20, 100); tft.print("Turn the power off");
    tft.setCursor(20, 124); tft.print("and on again");
    tft.setTextSize(1);
    tft.setTextColor(getTftTextMuted(), getTftCardBg());
    tft.setCursor(20, 162); tft.print("If it keeps happening, flash the board again.");
    tft.setCursor(20, 176); tft.print("Card reading still works without Wi-Fi.");
    soundBeep();
  }

  drawBentoBottomBar(hostApReady ? "Starting up..." : "Wi-Fi is off, the rest still works");
  delay(3000);
}

// --- ชิ้นส่วนเพิ่มเติมสำหรับหน้าจอแบบใหม่ ---

// [113.0.0] เพิ่ม: ชุดชิ้นส่วนสำหรับหน้าจอแบบใหม่
// ตัดข้อความให้พอดีความกว้างที่ให้มา (ฟอนต์ในตัวกว้างตัวละ 6 พิกเซลต่อขนาด 1)
// [113.4.0] เพิ่ม: ชื่อร้านสำหรับขึ้นจอ ลำดับการถอย ชื่ออังกฤษ > ส่วน ASCII ของชื่อจริง > Shop N
//           ประกันว่าจอจะไม่มีวันได้รับข้อความที่ฟอนต์วาดไม่ได้
String shopScreenName(int i) {
  String s = asciiOnly(shops[i].screen);
  if (s.length() == 0) s = asciiOnly(shops[i].name);
  if (s.length() == 0) s = "Shop " + String(i + 1);
  return s;
}

String fitLabel(const String &raw, int maxChars) {
  if ((int)raw.length() <= maxChars) return raw;
  if (maxChars <= 1) return raw.substring(0, maxChars);
  return raw.substring(0, maxChars - 1) + ".";
}

// หัวข้อเล็ก ๆ มุมบนซ้ายของการ์ด บอกว่าการ์ดนี้คืออะไร
void drawCardLabel(int x, int y, const char* label) {
  tft.setTextColor(getTftTextMuted(), getTftCardBg());
  tft.setTextSize(1);
  tft.setCursor(x, y);
  tft.print(label);
}

// จุดกลมบอกสถานะ ใช้แทนคำว่า ONLINE/OFFLINE ที่ยาวเกินไป
void drawStatusDot(int cx, int cy, bool good) {
  tft.fillCircle(cx, cy, 4, good ? getTftAccentGreen() : getTftAccentRose());
}

// แถบความคืบหน้า ใช้บอกว่าวันนี้จ่ายไปแล้วกี่ส่วนของทั้งหมด
void drawProgressBar(int x, int y, int w, int h, int pct) {
  if (pct < 0) pct = 0;
  if (pct > 100) pct = 100;
  // [113.3.0] แก้: สี่เหลี่ยมมุมโค้งไม่ลงสีที่มุมทั้งสี่ ค่าเก่าจึงค้างอยู่ตรงนั้น
  //           ล้างกรอบสี่เหลี่ยมเต็มก่อนหนึ่งครั้ง แถบนี้วาดเฉพาะตอนยอดเปลี่ยน
  //           ไม่ได้วาดทุกวินาที จึงไม่ทำให้กะพริบ
  tft.fillRect(x, y, w, h, getTftCardBg());
  tft.fillRoundRect(x, y, w, h, h / 2, getTftBg());
  int fillW = (w * pct) / 100;
  if (fillW < 2 && pct > 0) fillW = 2;
  if (fillW > 0) tft.fillRoundRect(x, y, fillW, h, h / 2, getTftAccentGreen());
}

// --- หน้าจอเต็ม: สามหน้าหลัก โหมดพักจอ ผลการสแกน และหน้าเครดิต ---
// ออกแบบใหม่ให้คนที่ไม่ใช่ช่างอ่านออกในสายตาเดียว
// หน้า 1 ยอดวันนี้ | หน้า 2 ร้านค้าและจุดบริการ | หน้า 3 ข้อมูลเครื่อง
// [113.0.0] แก้: ออกแบบสามหน้าหลักใหม่ให้คนที่ไม่ใช่ช่างอ่านออกในสายตาเดียว
//           หน้า 1 ยอดวันนี้ | หน้า 2 ร้านค้าและจุดบริการ | หน้า 3 ข้อมูลเครื่อง
void renderHostPage(bool fullRedraw) {
  if (isLiveScanDisplaying) return;
  if (isCreditActive) { renderDeveloperCredit(); return; }
  if (isScreensaverActive) { renderScreensaver(fullRedraw); return; }
  if (currentHostPage < 0 || currentHostPage >= TOTAL_PAGES) currentHostPage = 0;

  ledStandby();

  int usedCount = 0;
  int shopCounts[4] = {0, 0, 0, 0};
  for (const auto& s : db) {
    if (s.claimed) {
      usedCount++;
      if (s.station >= 1 && s.station <= 4) shopCounts[s.station - 1]++;
    }
  }

  if (fullRedraw) tft.fillScreen(getTftBg());

  // ==========================================================================
  // หน้า 1 — ยอดวันนี้ สามช่องใหญ่ ตัวเลขโต ๆ อ่านจากไกลได้
  // ==========================================================================
  if (currentHostPage == 0) {
    if (fullRedraw) {
      drawHostTopBar("TODAY", 1);
      drawBentoCard(6, 32, 150, 88, getTftCardBorder(), getTftCardBg());
      drawCardLabel(14, 40, "MEALS SERVED");
      drawBentoCard(164, 32, 150, 88, getTftCardBorder(), getTftCardBg());
      drawCardLabel(172, 40, "BAHT PAID");
      drawBentoCard(6, 126, 308, 82, getTftCardBorder(), getTftCardBg());
      drawCardLabel(14, 134, "SERVICE");
      drawBentoBottomBar("Click: next page    Double click: sleep");
    }

    // [113.2.0] แก้: วาดซ้ำเฉพาะช่องที่ค่าเปลี่ยนจริง ของเดิมล้างแล้ววาดใหม่ทุกวินาที
    //           ทั้งที่ตัวเลขส่วนใหญ่ไม่ได้เปลี่ยน จอจึงกะพริบตลอดเวลา
    static int lastUsed = -1, lastTotal = -1;
    static String lastClock = "", lastDate = "";
    static int lastOpen = -1;

    // ช่องซ้าย: จำนวนจานที่จ่ายไปแล้ว พร้อมแถบความคืบหน้า
    if (fullRedraw || usedCount != lastUsed || (int)db.size() != lastTotal) {
      drawFixedText(14, 56, 4, getTftTextMain(), getTftCardBg(), 4, "%d", usedCount);
      drawFixedText(14, 92, 1, getTftTextMuted(), getTftCardBg(), 20,
                    "of %d students", (int)db.size());
      int pct = (db.size() > 0) ? (usedCount * 100) / (int)db.size() : 0;
      drawProgressBar(14, 106, 134, 6, pct);

      // ช่องขวา: เป็นเงินเท่าไร เปลี่ยนพร้อมกันกับจำนวนจานเสมอ
      drawFixedText(172, 56, 4, getTftAccentGreen(), getTftCardBg(), 5, "%d", usedCount * 35);
      drawFixedText(172, 92, 1, getTftTextMuted(), getTftCardBg(), 20, "35 baht per student");

      lastUsed = usedCount;
      lastTotal = (int)db.size();
    }

    // ช่องล่าง: นาฬิกาเดินทุกวินาที จึงเป็นจุดที่คนเห็นการกะพริบชัดที่สุด
    // เขียนทับที่เดิมอย่างเดียว ไม่ล้างพื้นก่อน รูปแบบ HH:MM:SS ยาวคงที่แปดตัวเสมอ
    String nowClock = getTimeOnlyStr();
    if (fullRedraw || nowClock != lastClock) {
      drawFixedText(14, 150, 4, getTftTextMain(), getTftCardBg(), 8, "%s", nowClock.c_str());
      lastClock = nowClock;
    }

    String nowDate = getDateFormattedStr();
    if (fullRedraw || nowDate != lastDate) {
      drawFixedText(14, 186, 1, getTftTextMuted(), getTftCardBg(), 24, "%s", nowDate.c_str());
      lastDate = nowDate;
    }

    bool isOpen = isWithinServiceTime();
    if (fullRedraw || (int)isOpen != lastOpen) {
      char hours[16];
      snprintf(hours, sizeof(hours), "%02d:%02d-%02d:%02d",
               serviceStartHour, serviceStartMin, serviceEndHour, serviceEndMin);
      tft.fillRect(210, 148, 100, 48, getTftCardBg());
      drawBentoPillBadge(214, 152, 94, 22, isOpen ? "OPEN" : "CLOSED",
                         isTftDarkMode ? 0x0000 : BENTO_WHITE,
                         isOpen ? getTftAccentGreen() : getTftAccentRose());
      tft.setTextColor(getTftTextMuted(), getTftCardBg());
      tft.setTextSize(1);
      // ให้อยู่บรรทัดฐานเดียวกับวันที่ทางซ้าย จะได้ดูเป็นแถวเดียวกัน
      tft.setCursor(214 + (94 - (int)strlen(hours) * 6) / 2, 186);
      tft.print(hours);
      lastOpen = (int)isOpen;
    }
  }
  // ==========================================================================
  // หน้า 2 — ร้านค้าและจุดบริการ สี่ช่อง เจ้าของร้านดูยอดของตัวเองได้ทันที
  // ==========================================================================
  else if (currentHostPage == 1) {
    if (fullRedraw) {
      drawHostTopBar("SHOPS", 2);
      drawBentoBottomBar("Click: next page    Double click: sleep");
    }

    int coords[4][2] = { {6, 32}, {164, 32}, {6, 122}, {164, 122} };
    static int waitDots = 0;
    if (!fullRedraw) waitDots = (waitDots + 1) % 4;

    for (int i = 0; i < 4; i++) {
      int x = coords[i][0], y = coords[i][1], w = 150, h = 86;

      if (fullRedraw) {
        drawBentoCard(x, y, w, h, getTftCardBorder(), getTftCardBg());

        // ชื่อร้านมาก่อน เพราะเจ้าของร้านมองหาชื่อตัวเอง ไม่ได้มองหาเลขจุดบริการ
        // เต็มความกว้างการ์ด ไม่มีอะไรมาวาดทับภายหลัง
        // ชื่อร้านเปลี่ยนได้เฉพาะตอนบันทึกจากหน้าเว็บ ซึ่งสั่งวาดใหม่ทั้งจออยู่แล้ว
        tft.setTextColor(getTftTextMain(), getTftCardBg());
        tft.setTextSize(1);
        // [113.4.0] แก้: เดิมเอาชื่อร้านภาษาไทยมาวาดตรง ๆ จอจึงขึ้นสัญลักษณ์มั่ว
        //           และกว้างกว่าที่นับไว้จนล้นไปทับของข้างเคียง
        drawFixedText(x + 8, y + 7, 1, getTftTextMain(), getTftCardBg(), 22,
                      "%s", shopScreenName(i).c_str());
      }

      // [113.2.0] แก้: ยอดของร้านเคยวาดเฉพาะตอนวาดใหม่ทั้งจอ พอมีคนมารับอาหาร
      //           ขณะเปิดหน้านี้ค้างไว้ ตัวเลขจึงไม่ขยับจนกว่าจะมีอะไรมาสั่งวาดใหม่
      //           ย้ายออกมาข้างนอก แล้ววาดซ้ำเฉพาะตอนค่าเปลี่ยนจริง
      static int lastShopCount[4] = {-1, -1, -1, -1};
      if (fullRedraw || shopCounts[i] != lastShopCount[i]) {
        // ยอดของร้าน ตัวเลขจานใหญ่สุดในการ์ด อ่านได้จากอีกฝั่งของโรงอาหาร
        // ตัวเลขกว้างคงที่สามหลัก ป้ายกำกับจึงอยู่กับที่ ไม่ขยับตามจำนวนหลัก
        drawFixedText(x + 8, y + 36, 3, getTftTextMain(), getTftCardBg(), 3,
                      "%d", shopCounts[i]);
        drawFixedText(x + 68, y + 38, 1, getTftTextMuted(), getTftCardBg(), 6, "meals");
        drawFixedText(x + 68, y + 52, 1, getTftAccentGreen(), getTftCardBg(), 10,
                      "%d baht", shopCounts[i] * 35);

        lastShopCount[i] = shopCounts[i];
      }

      // [113.3.0] แก้: สองแถวนี้เคยล้างพื้นแล้ววาดใหม่ทุกวินาทีแม้ค่าไม่เปลี่ยน
      //           ซึ่งเป็นต้นเหตุการกะพริบบนหน้านี้ ตอนนี้แตะเฉพาะตอนค่าเปลี่ยนจริง
      static int lastOnlineState[4] = {-1, -1, -1, -1};
      static int lastBars[4]  = {-1, -1, -1, -1};
      static int lastBatt[4]  = {-1, -1, -1, -1};
      static int lastDots[4]  = {-1, -1, -1, -1};

      bool online = stationNodes[i].isOnline;
      // นับจำนวนขีดจากคุณภาพสัญญาณ ใช้เกณฑ์เดียวกับ drawSignalBars
      // เทียบด้วยจำนวนขีด ไม่ใช่ค่า dBm ดิบ ๆ จอจะได้ไม่วาดใหม่ทุกครั้งที่สัญญาณขยับนิดเดียว
      int  q      = calculateSignalQuality(stationNodes[i].rssi);
      int  bars   = !online ? 0 : (q >= 85 ? 4 : q >= 60 ? 3 : q >= 35 ? 2 : 1);
      int  batt   = online ? getHostBatteryPercentage(stationNodes[i].systemVoltage) : 0;
      bool stateChanged = (fullRedraw || (int)online != lastOnlineState[i]);

      if (stateChanged) {
        // [113.8.0] แก้: เปลี่ยนคำว่า Point เป็น Station ให้ตรงกับชื่อที่ใช้ทั้งระบบ
        // ชื่อ "Station N" ไม่เคยเปลี่ยน วาดตอนเริ่มกับตอนสลับสถานะก็พอ
        drawStatusDot(x + 12, y + 25, online);
        drawFixedText(x + 22, y + 22, 1, getTftTextMuted(), getTftCardBg(), 9,
                      "Station %d", i + 1);
        lastOnlineState[i] = (int)online;
        lastBars[i] = -1;   // บังคับให้แถวล่างวาดใหม่ เพราะเพิ่งเปลี่ยนรูปแบบ
        lastBatt[i] = -1;
        lastDots[i] = -1;
        tft.fillRect(x + 8, y + 66, w - 16, 14, getTftCardBg());
      }

      if (online) {
        if (stateChanged || bars != lastBars[i]) {
          drawSignalBars(x + 8, y + 68, stationNodes[i].rssi, true, getTftCardBg());
          drawFixedText(x + 40, y + 70, 1, getTftTextMuted(), getTftCardBg(), 7, "signal");
          lastBars[i] = bars;
        }
        if (stateChanged || batt != lastBatt[i]) {
          drawFixedText(x + 92, y + 70, 1, getTftTextMuted(), getTftCardBg(), 4, "%d%%", batt);
          drawMiniBattery(x + 120, y + 68, batt);
          lastBatt[i] = batt;
        }
      } else if (stateChanged || waitDots != lastDots[i]) {
        // จุดไข่ปลาวิ่งบอกว่าเครื่องยังตามหาอยู่ ความยาวคงที่จึงไม่ต้องล้างพื้น
        char wait[12] = "Waiting";
        for (int d = 0; d <= waitDots; d++) strcat(wait, ".");
        drawFixedText(x + 8, y + 70, 1, getTftAccentRose(), getTftCardBg(), 11, "%s", wait);
        lastDots[i] = waitDots;
      }
    }
  }
  // ==========================================================================
  // หน้า 3 — ข้อมูลเครื่อง สำหรับคนดูแลระบบ ไม่ใช่สำหรับเจ้าของร้าน
  // ==========================================================================
  else {
    if (fullRedraw) {
      drawHostTopBar("SYSTEM", 3);
      drawBentoCard(6, 32, 308, 84, getTftCardBorder(), getTftCardBg());
      drawCardLabel(14, 40, "LAST CARD TAP");
      drawBentoCard(6, 122, 150, 86, getTftCardBorder(), getTftCardBg());
      drawCardLabel(14, 130, "NETWORK");
      drawBentoCard(164, 122, 150, 86, getTftCardBorder(), getTftCardBg());
      drawCardLabel(172, 130, "DEVICE");

      tft.setTextColor(getTftTextMain(), getTftCardBg());
      tft.setTextSize(1);
      tft.setCursor(14, 148); tft.print("Wi-Fi  MCU_CANTEEN");
      tft.setCursor(14, 164); tft.print("Page   192.168.4.1");
      tft.setCursor(14, 180); tft.print("Radio  channel 1");
      tft.setTextColor(getTftTextMuted(), getTftCardBg());
      tft.setCursor(14, 192); tft.print("4 stations linked");

      drawBentoBottomBar("Click: next page    Double click: sleep");
    }

    // [113.2.0] แก้: วาดผลการแตะบัตรซ้ำเฉพาะตอนมีการแตะใหม่จริง
    static String lastShownRef = "\x01";
    String stamp = lastScannedRef + "|" + lastScannedStatus + "|" + lastScannedUID;
    bool scanChanged = (fullRedraw || stamp != lastShownRef);
    if (scanChanged) lastShownRef = stamp;

    if (scanChanged) {
      tft.fillRect(12, 54, 296, 58, getTftCardBg());
      if (lastScannedUID != "-" && lastScannedUID.length() > 0) {
        tft.setTextColor(getTftTextMain(), getTftCardBg());
        tft.setTextSize(3);
        tft.setCursor(14, 56);
        // รหัสนิสิตมาจากไฟล์ที่นำเข้า จึงกรองก่อนวาดเผื่อมีอักขระที่ฟอนต์ไม่มี
        String sid = asciiOnly(lastScannedStudentId);
        if (sid.length() == 0 || sid == "-") sid = "Unknown card";
        tft.print(sid);

        tft.setTextSize(1);
        tft.setTextColor(getTftTextMuted(), getTftCardBg());
        tft.setCursor(14, 86);
        tft.printf("Station %d   card %s", lastScannedStation, maskUID(lastScannedUID).c_str());

        const char* word; uint16_t tone;
        if (lastScannedStatus == "APPROVED")         { word = "SERVED";         tone = getTftAccentGreen(); }
        else if (lastScannedStatus == "DUPLICATE")   { word = "ALREADY SERVED"; tone = getTftAccentYellow(); }
        else if (lastScannedStatus == "TIME_CLOSED") { word = "CLOSED NOW";     tone = getTftAccentYellow(); }
        else                                         { word = "NOT ON LIST";    tone = getTftAccentRose(); }
        drawBentoPillBadge(14, 98, 130, 14, word,
                           isTftDarkMode ? 0x0000 : BENTO_WHITE, tone);

        // เลขอ้างอิงยาวกว่าที่การ์ดรับไหว จึงโชว์ท้ายเลข ซึ่งเป็นส่วนที่ไม่ซ้ำกัน
        String ref = lastScannedRef;
        if (ref.length() > 24) ref = "." + ref.substring(ref.length() - 23);
        tft.setTextColor(getTftTextMuted(), getTftCardBg());
        tft.setCursor(152, 101);
        tft.print(ref);
      } else {
        tft.setTextColor(getTftTextMuted(), getTftCardBg());
        tft.setTextSize(2);
        tft.setCursor(14, 72);
        tft.print("No card tapped yet");
      }
    }

    // [113.2.0] แก้: ตัวเลขของเครื่องวาดซ้ำเฉพาะตอนค่าเปลี่ยน
    //           อุณหภูมิขยับตลอดเวลา ถ้าล้างแล้ววาดใหม่ทุกรอบจอจะกะพริบ
    static int lastDbSize = -1, lastAdmins = -1, lastTempC = -999, lastHeapKB = -1;
    float cTemp = getChipTemperature();
    int tempC = (int)(cTemp + 0.5f);
    int heapKB = ESP.getFreeHeap() / 1024;

    if (fullRedraw || (int)db.size() != lastDbSize || (int)adminUsers.size() != lastAdmins) {
      drawFixedText(172, 148, 1, getTftTextMain(), getTftCardBg(), 22,
                    "Students %d", (int)db.size());
      drawFixedText(172, 164, 1, getTftTextMain(), getTftCardBg(), 22,
                    "Staff    %d of 3", (int)adminUsers.size());
      lastDbSize = (int)db.size();
      lastAdmins = (int)adminUsers.size();
    }
    if (fullRedraw || tempC != lastTempC) {
      drawFixedText(172, 180, 1,
                    (cTemp < 65.0f) ? getTftTextMain() : getTftAccentYellow(),
                    getTftCardBg(), 22, "Chip     %d C", tempC);
      lastTempC = tempC;
    }
    // หน่วยความจำว่างแกว่งเป็นไบต์ตลอด จึงถือว่าเปลี่ยนเมื่อขยับเกินสองกิโล
    if (fullRedraw || abs(heapKB - lastHeapKB) >= 2) {
      drawFixedText(172, 192, 1, getTftTextMuted(), getTftCardBg(), 22,
                    "Free memory %d KB", heapKB);
      lastHeapKB = heapKB;
    }
  }
}

// ============================================================================
// SCREENSAVER
// ============================================================================
void renderScreensaver(bool fullRedraw) {
  int usedCount = 0;
  for (const auto& s : db) if (s.claimed) usedCount++;

  static String lastHostClock = "";

  if (fullRedraw) {
    ledOff();
    tft.fillScreen(getTftBg());
    lastHostClock = "";
    drawHostTopBar("MCU CANTEEN");

    drawBentoCard(20, 40, 280, 156, getTftCardBorder(), getTftCardBg());

    // สรุปยอดวันนี้กับแถบความคืบหน้า วาดอยู่ที่เดียวข้างล่าง
    // ถ้าวาดตรงนี้ด้วยจะได้สองบรรทัดคนละตำแหน่ง
    drawBentoBottomBar("Tap a card or press the button to wake");
  }

  // [113.5.0] แก้: ทุกบรรทัดบนหน้านี้จัดกึ่งกลางที่ x = 160 เหมือนกันหมด
  //           ของเดิมบรรทัดสีเขียวชิดซ้ายที่ x = 62 จึงเยื้องไม่ตรงกับนาฬิกาและวันที่
  static String lastSaverDate = "";
  static int lastSaverUsed = -1;

  // นาฬิกาตัวโต ยาวคงที่แปดตัว
  String curTime = getTimeOnlyStr();
  if (fullRedraw || curTime != lastHostClock) {
    lastHostClock = curTime;
    drawCenteredText(160, 68, 5, getTftTextMain(), getTftCardBg(), 8, "%s", curTime.c_str());
  }

  // วันที่ อยู่ใต้นาฬิกา เปลี่ยนตอนข้ามวันจึงต้องวาดซ้ำได้ด้วย
  String dateStr = getDateFormattedStr();
  if (fullRedraw || dateStr != lastSaverDate) {
    lastSaverDate = dateStr;
    drawCenteredText(160, 124, 1, getTftTextMuted(), getTftCardBg(), 20, "%s", dateStr.c_str());
  }

  // [113.2.0] แก้: ยอดวันนี้บนหน้าพักจอเคยวาดครั้งเดียวตอนเข้าโหมด
  //           ถ้ามีคนมารับอาหารระหว่างพักจอ ตัวเลขจะค้างอยู่ที่ค่าเก่า
  if (fullRedraw || usedCount != lastSaverUsed) {
    lastSaverUsed = usedCount;
    drawCenteredText(160, 146, 1, getTftAccentGreen(), getTftCardBg(), 34,
                     "%d of %d served   %d baht", usedCount, (int)db.size(), usedCount * 35);
    int pct = (db.size() > 0) ? (usedCount * 100) / (int)db.size() : 0;
    drawProgressBar(60, 170, 200, 6, pct);
  }
}

// ============================================================================
// LIVE SCAN ALERT (FULL-SCREEN COLOR TAKEOVER & ADAPTIVE FEEDBACK)
// ============================================================================
void displayHostLiveScan(String uid, String studentId, String status, int stId) {
  isLiveScanDisplaying = true;
  liveScanHoldUntil = millis() + 4500;

  uint16_t screenBg;
  uint16_t cardBg;
  uint16_t bannerBg;
  uint16_t bannerFg;
  uint16_t accentColor;
  uint16_t textColor = BENTO_WHITE;
  uint16_t textMuted;
  const char* headerTitle;
  const char* footerDesc;

  if (status == "APPROVED") {
    ledApproved();
    screenBg    = 0x02E5;             // พื้นหลังจอเฉดเขียวเข้ม
    cardBg      = 0x01C3;             // พื้นหลังการ์ดโทนเขียวมรกตลึก
    bannerBg    = BENTO_NEON_GREEN;   // แถบแบนเนอร์สีเขียวนีออน
    bannerFg    = 0x0000;             // ตัวอักษรสีดำ
    accentColor = BENTO_NEON_GREEN;
    textMuted   = 0x87F0;             // ข้อความกำกับสีเขียวมิ้นต์
    headerTitle = "APPROVED";
    footerDesc  = "Meal paid, 35 baht";
  } 
  else if (status == "DUPLICATE") {
    ledDuplicate();
    screenBg    = 0x8200;             // พื้นหลังจอเฉดส้มอิฐเข้ม
    cardBg      = 0x4900;             // พื้นหลังการ์ดโทนส้มเข้ม
    bannerBg    = ST77XX_ORANGE;      // แถบแบนเนอร์สีส้มสด
    bannerFg    = 0x0000;             // ตัวอักษรสีดำ
    accentColor = ST77XX_ORANGE;
    textMuted   = 0xFDC0;             // ข้อความกำกับสีส้มอ่อน
    headerTitle = "ALREADY SERVED";
    footerDesc  = "This student already ate today";
  } 
  else if (status == "TIME_CLOSED") {
    ledDuplicate();
    screenBg    = 0x6200;             // พื้นหลังโทนส้มอมน้ำตาล
    cardBg      = 0x3900;             // พื้นหลังการ์ดโทนน้ำตาลเข้ม
    bannerBg    = BENTO_NEON_YELLOW;  // แถบแบนเนอร์สีเหลืองเตือนภัย
    bannerFg    = 0x0000;
    accentColor = BENTO_NEON_YELLOW;
    textMuted   = 0xFEE0;
    headerTitle = "CLOSED NOW";
    footerDesc  = "Outside the service hours";
  } 
  else {
    ledRejected();
    screenBg    = 0x8000;             // พื้นหลังจอเฉดแดงทึบเข้ม
    cardBg      = 0x4800;             // พื้นหลังการ์ดโทนแดงเข้ม
    bannerBg    = BENTO_NEON_ROSE;    // แถบแบนเนอร์สีแดงสด
    bannerFg    = BENTO_WHITE;        // ตัวอักษรสีขาว
    accentColor = BENTO_NEON_ROSE;
    textMuted   = 0xFCAE;             // ข้อความกำกับสีชมพูอ่อน
    headerTitle = "NOT ON THE LIST";
    footerDesc  = "This card is not registered";
  }

  tft.fillScreen(screenBg);

  tft.fillRect(0, 0, 320, 36, bannerBg);
  tft.setTextSize(3);
  tft.setTextColor(bannerFg, bannerBg);
  int titleLen = strlen(headerTitle) * 18;
  int titleX = max(4, (320 - titleLen) / 2);
  tft.setCursor(titleX, 7);
  tft.print(headerTitle);

  tft.fillRoundRect(8, 44, 304, 188, 8, cardBg);
  tft.drawRoundRect(8, 44, 304, 188, 8, accentColor);
  tft.drawRoundRect(9, 45, 302, 186, 7, accentColor);

  tft.setTextSize(1);
  tft.setTextColor(textMuted, cardBg);
  tft.setCursor(20, 54);
  tft.print("STATION");
  
  tft.setTextSize(2);
  tft.setTextColor(textColor, cardBg);
  tft.setCursor(20, 66);
  tft.printf("Station %d", stId);

  tft.drawFastHLine(20, 88, 280, accentColor);

  tft.setTextSize(1);
  tft.setTextColor(textMuted, cardBg);
  tft.setCursor(20, 96);
  tft.print("STUDENT ID");

  String cleanId = (studentId != "-" && studentId.length() > 0) ? studentId : "Unknown";
  tft.setTextSize(3);
  tft.setTextColor(textColor, cardBg);
  tft.setCursor(20, 110);
  tft.print(cleanId);

  tft.setTextSize(1);
  tft.setTextColor(textMuted, cardBg);
  tft.setCursor(20, 142);
  tft.print("CARD");

  tft.setTextSize(2);
  tft.setTextColor(textColor, cardBg);
  tft.setCursor(20, 154);
  tft.print(maskUID(uid));

  tft.fillRoundRect(16, 184, 288, 36, 6, bannerBg);
  tft.setTextSize(1);
  tft.setTextColor(bannerFg, bannerBg);
  int descLen = strlen(footerDesc) * 6;
  int descX = max(20, (320 - descLen) / 2);
  tft.setCursor(descX, 198);
  tft.print(footerDesc);
}

void renderDeveloperCredit() {
  tft.fillScreen(getTftBg());
  drawHostTopBar("ABOUT");

  drawBentoCard(10, 36, 300, 166, getTftCardBorder(), getTftCardBg());

  drawCardLabel(22, 48, "BUILT BY");
  tft.setTextColor(getTftTextMain(), getTftCardBg());
  tft.setTextSize(2);
  tft.setCursor(22, 64);
  tft.println(DEV_NAME);

  tft.setTextColor(getTftTextMuted(), getTftCardBg());
  tft.setTextSize(1);
  tft.setCursor(22, 92);
  tft.println(DEV_ROLE);
  tft.setCursor(22, 108);
  tft.println("Mahachulalongkornrajavidyalaya Phrae");

  tft.drawFastHLine(22, 126, 276, getTftCardBorder());

  tft.setTextColor(getTftTextMuted(), getTftCardBg());
  tft.setCursor(22, 140); tft.printf("Firmware  v%s\n", APP_VERSION);
  tft.setCursor(22, 156); tft.printf("Board     ESP32-S3 N16R8, %d MB PSRAM\n", ESP.getPsramSize() / 1024 / 1024);
  tft.setCursor(22, 172); tft.println("Screen    2.8 inch 320x240");

  drawBentoBottomBar("Press the button to go back");
}
